ClubRobotiqueECAM/Balises/Photos/2015-09-10 11.16.47.jpg

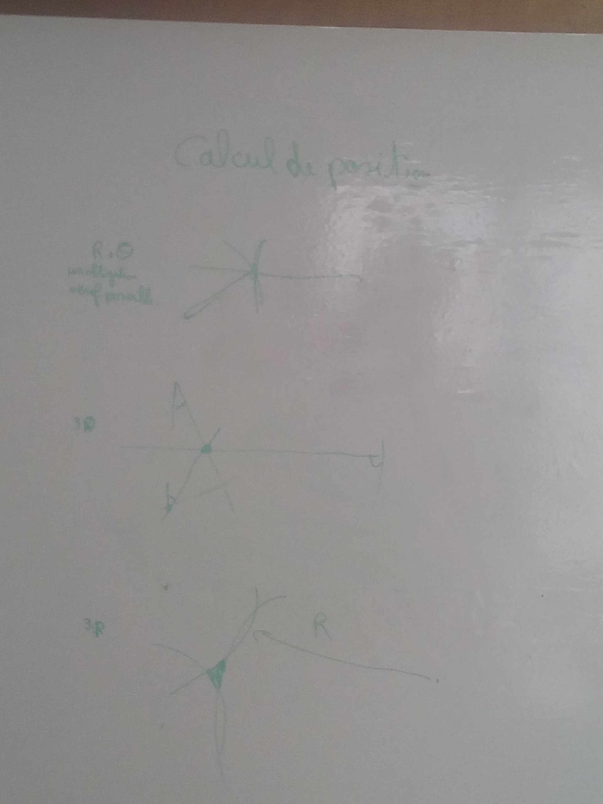
Photos/2015-09-10 11.16.47.jpg
