ClubRobotiqueECAM/Balises/Photos/2015-09-18 08.21.55.jpg

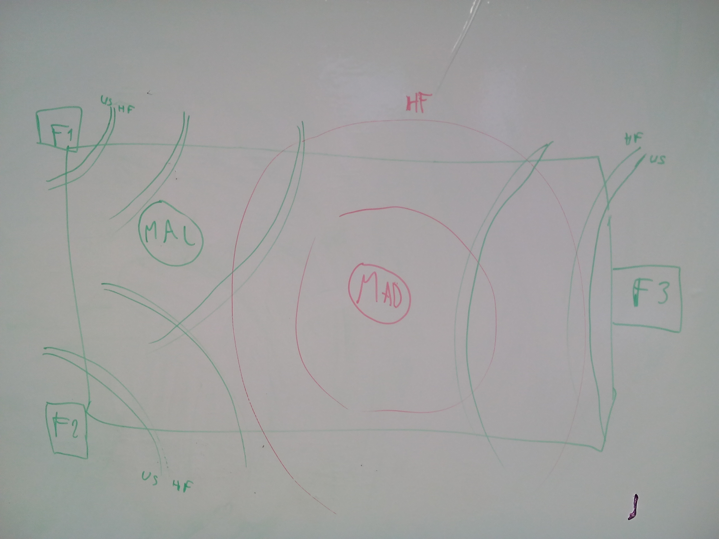
Photos/2015-09-18 08.21.55.jpg
