ClubRobotiqueECAM/Balises/Photos/2015-09-18 15.36.44.jpg

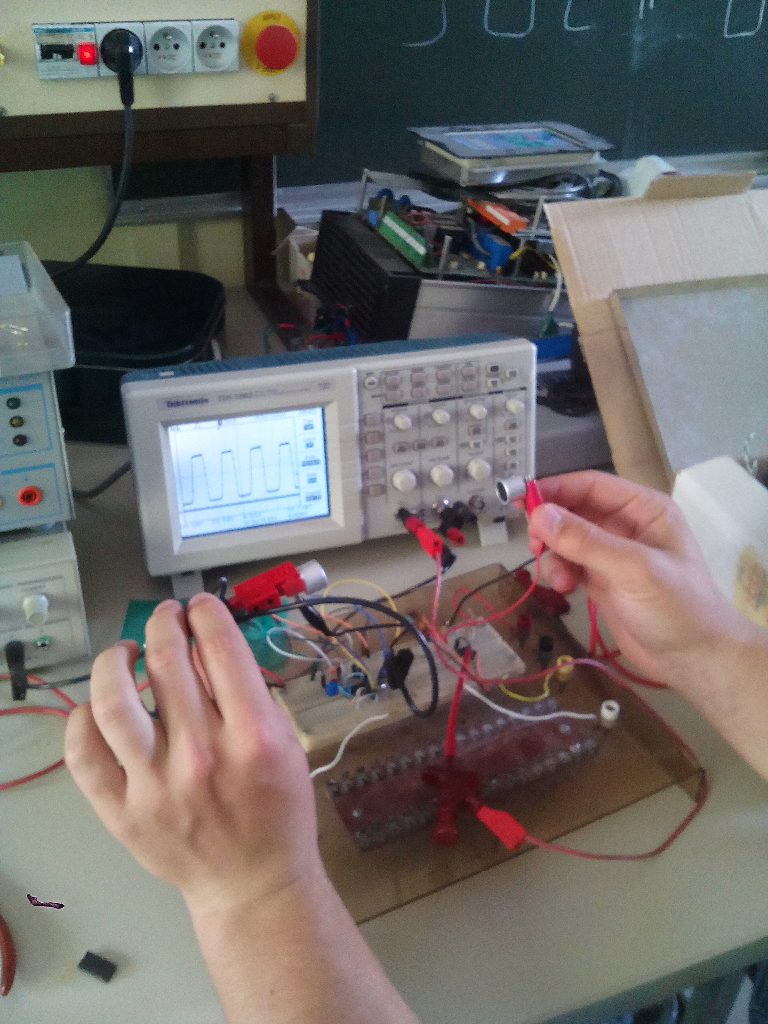
Photos/2015-09-18 15.36.44.jpg
