ClubRobotiqueECAM/Balises/Photos/2015-09-18 15.37.08.jpg

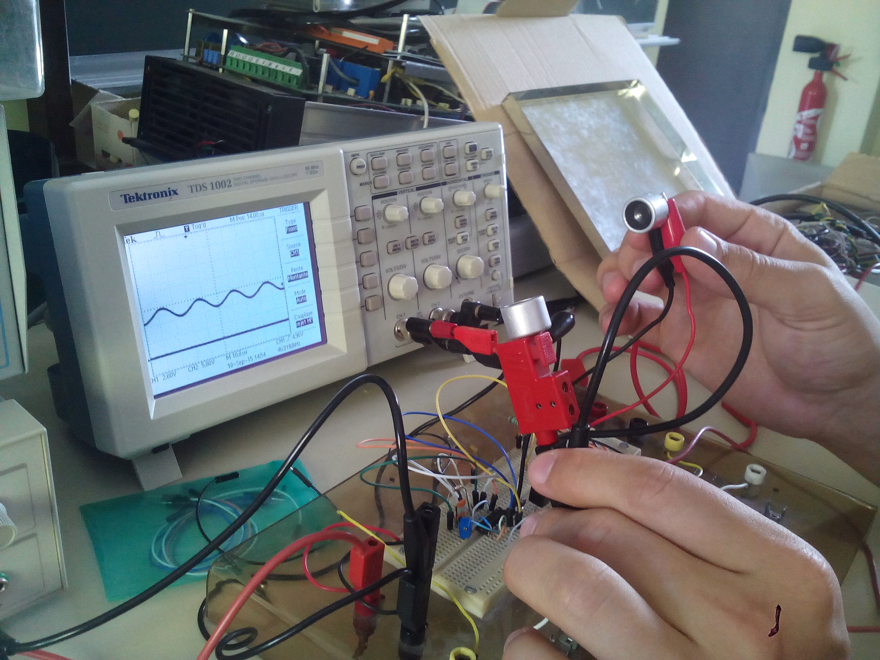
Photos/2015-09-18 15.37.08.jpg
