ClubRobotiqueECAM/Balises/Photos/2015-09-24 05-2 AO Proche.BMP

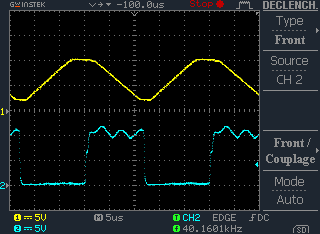
Photos/2015-09-24 05-2 AO Proche.BMP
