ClubRobotiqueECAM/Balises/Photos/2015-09-24 14.49.16.jpg

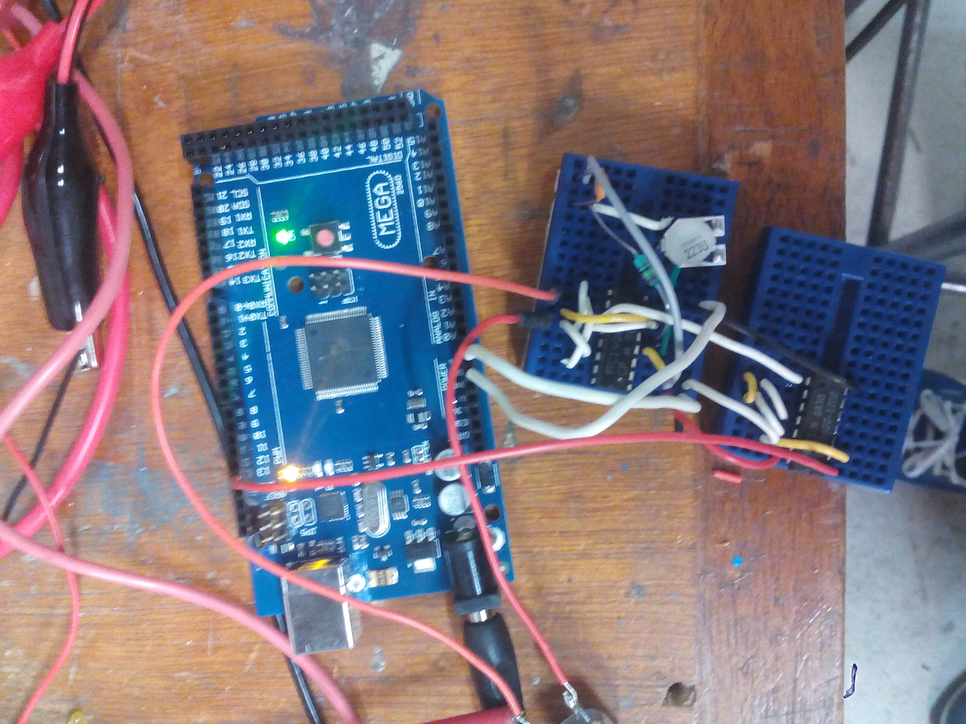
Photos/2015-09-24 14.49.16.jpg
