ClubRobotiqueECAM/Balises/Photos/2015-10-22 09.53.31.jpg

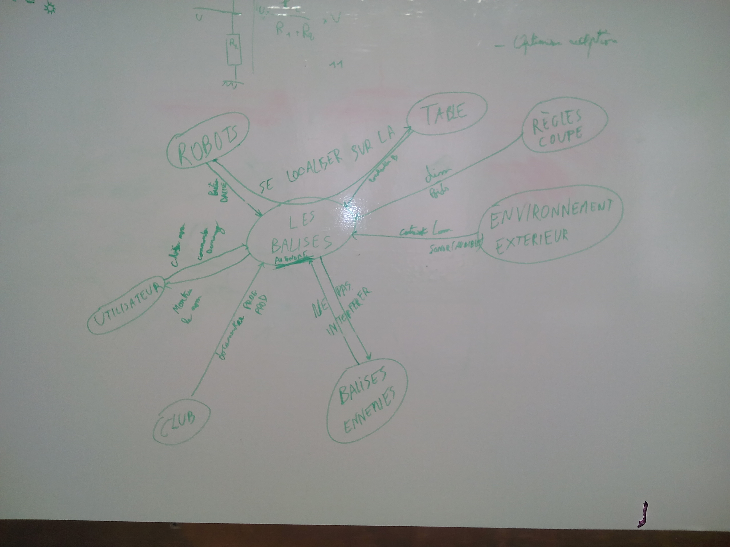
Photos/2015-10-22 09.53.31.jpg
