ClubRobotiqueECAM/Balises/Photos/2015-11-04 15.26.15.jpg

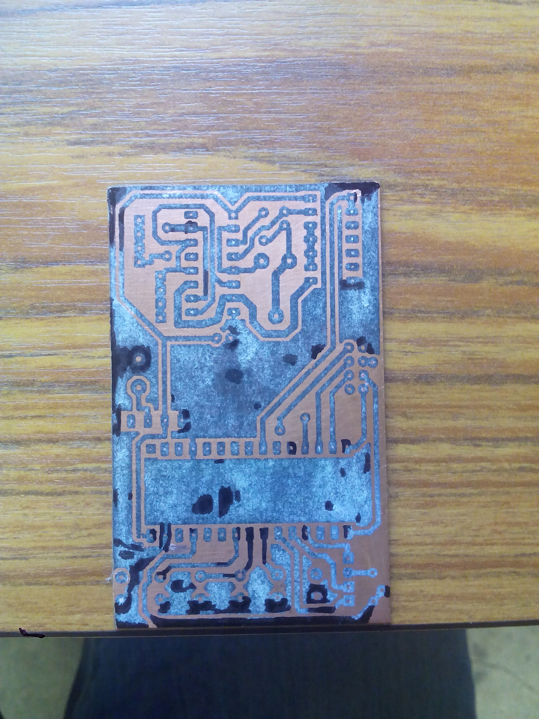
Photos/2015-11-04 15.26.15.jpg
