ClubRobotiqueECAM/Balises/Photos/2015-11-04 16.58.57.jpg

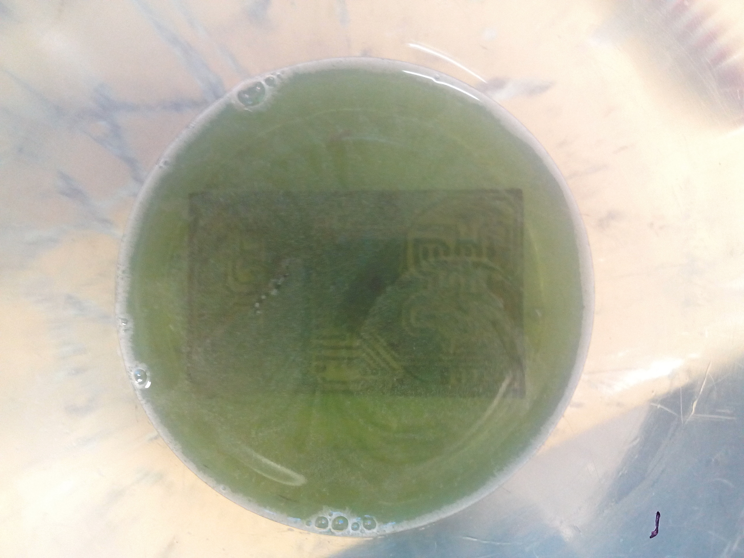
Photos/2015-11-04 16.58.57.jpg
