ClubRobotiqueECAM/Balises/Photos/2015-11-04 16.59.13.jpg

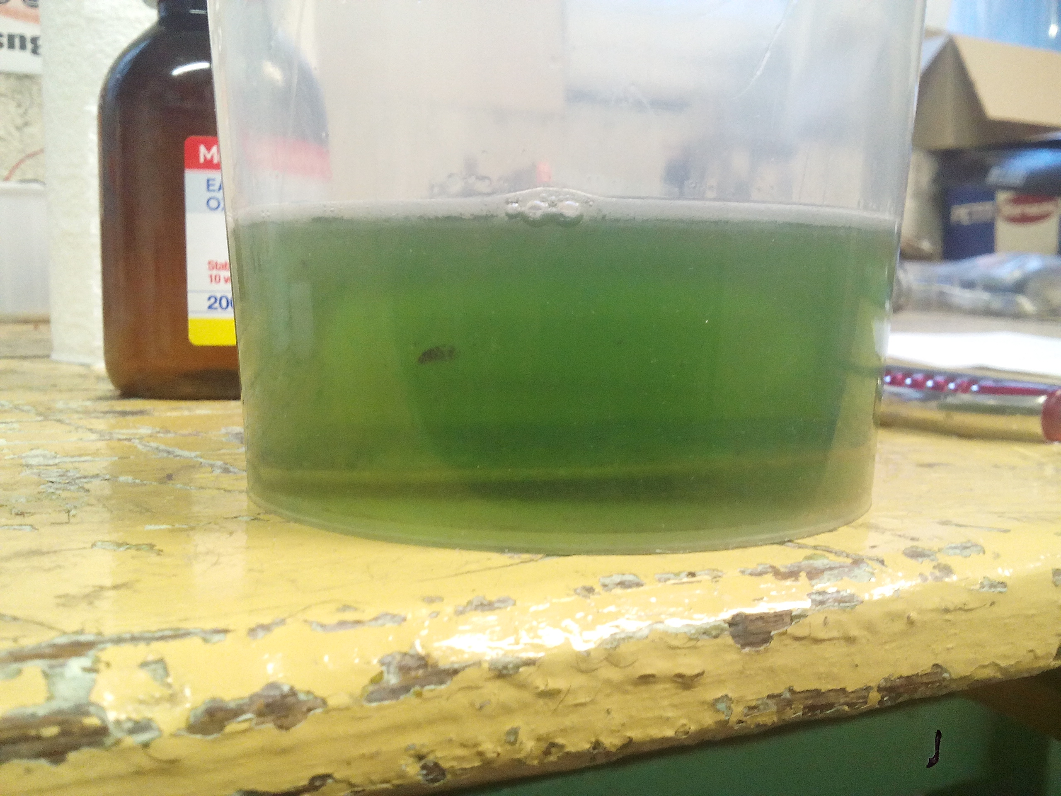
Photos/2015-11-04 16.59.13.jpg
