ClubRobotiqueECAM/Balises/Photos/2015-11-05 22.45.04.jpg

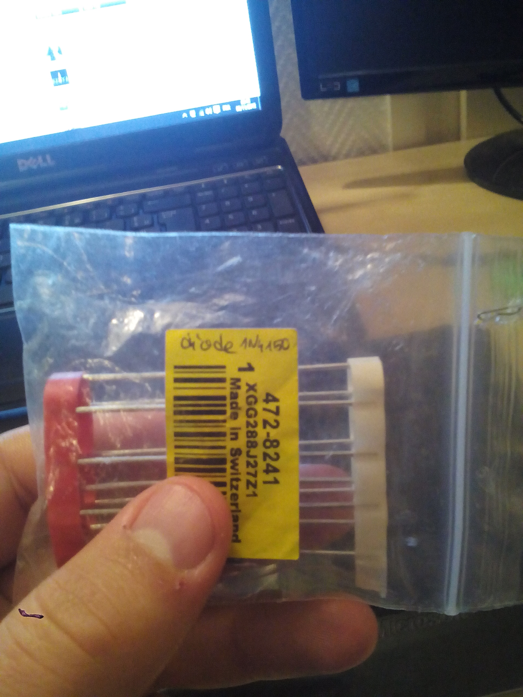
Photos/2015-11-05 22.45.04.jpg
