ClubRobotiqueECAM/Balises/Photos/2015-11-06 15.36.19.jpg

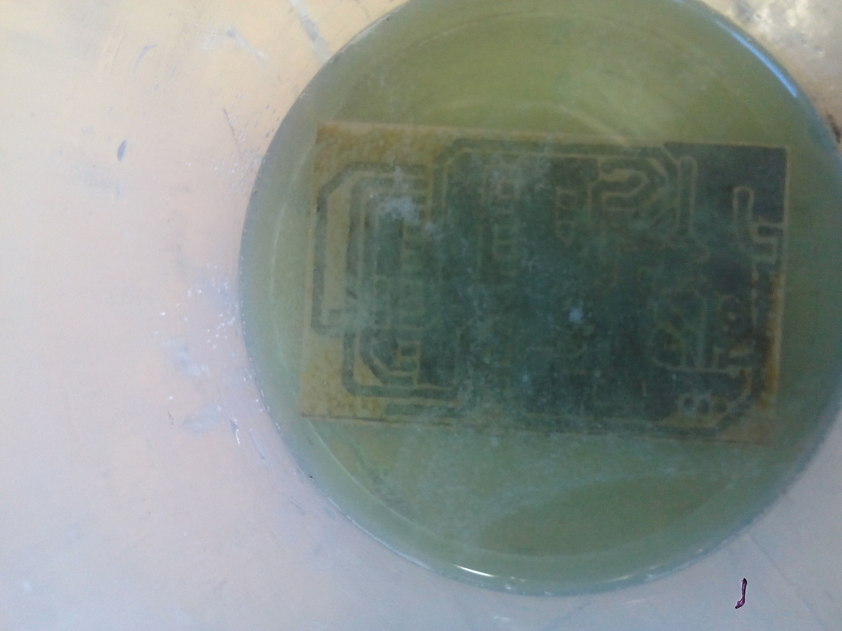
Photos/2015-11-06 15.36.19.jpg
