ClubRobotiqueECAM/Balises/Photos/2015-11-06 15.36.27.jpg

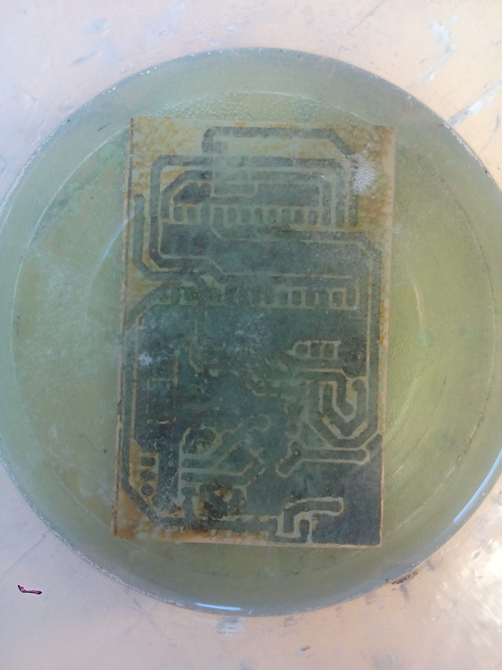
Photos/2015-11-06 15.36.27.jpg
