ClubRobotiqueECAM/Balises/Photos/2015-11-06 15.54.33.jpg

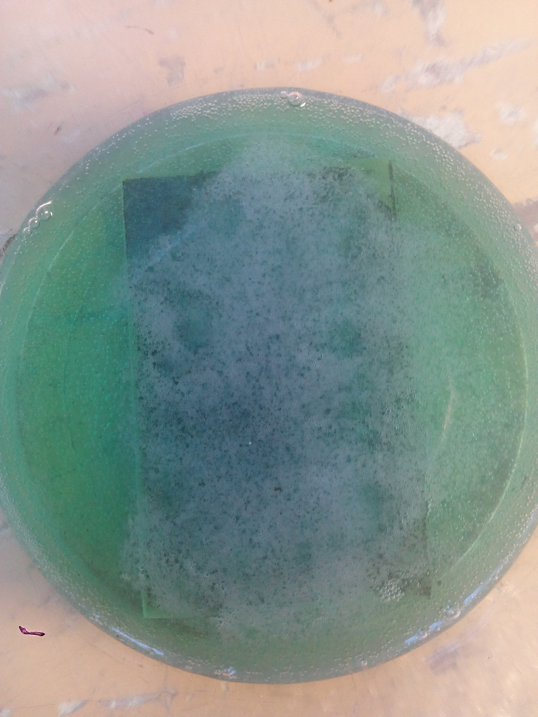
Photos/2015-11-06 15.54.33.jpg
