ClubRobotiqueECAM/Balises/Photos/2015-11-12 11.26.49.jpg

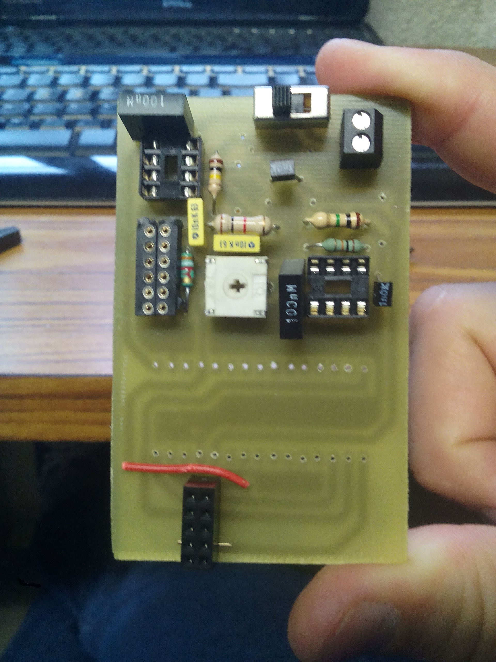
Photos/2015-11-12 11.26.49.jpg
