ClubRobotiqueECAM/Balises/Photos/2015-11-20 09.31.01 mot.jpg

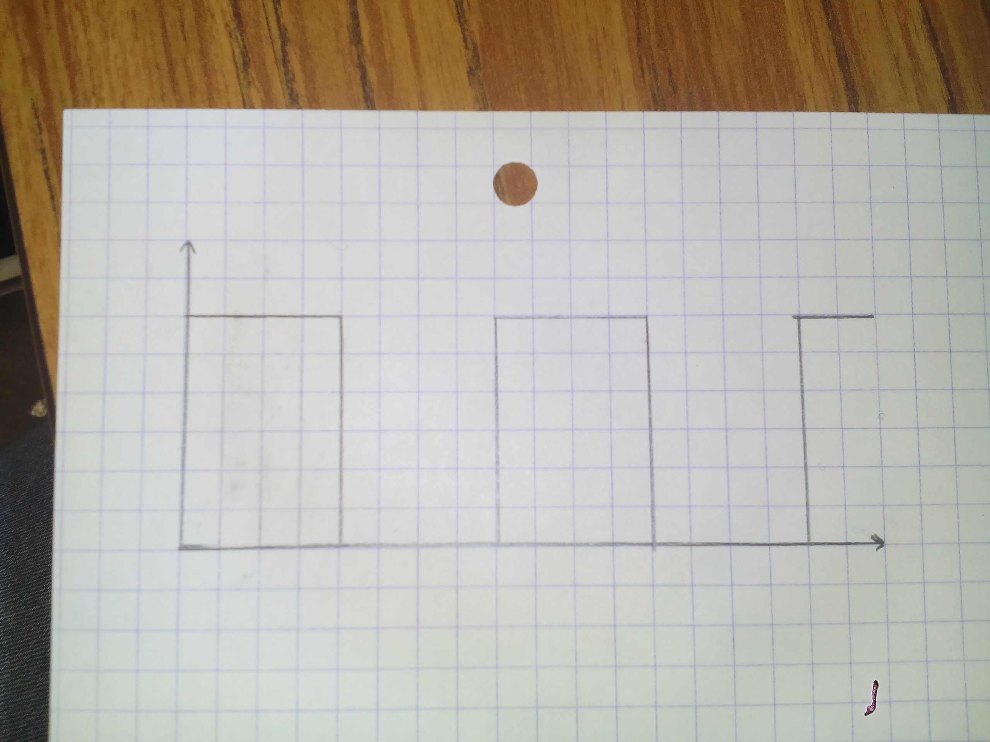
Photos/2015-11-20 09.31.01 mot.jpg
