ClubRobotiqueECAM/Balises/Photos/2015-11-20 09.34.17 porteuse.jpg

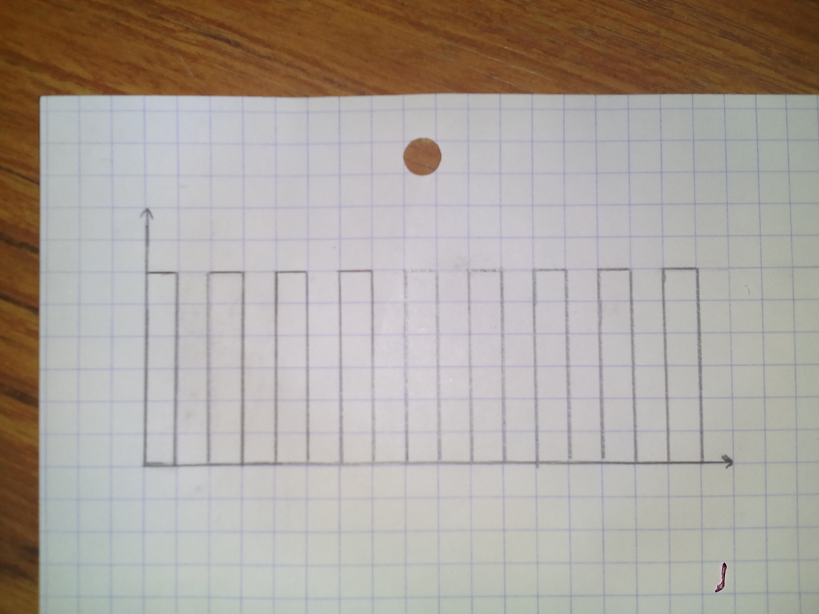
Photos/2015-11-20 09.34.17 porteuse.jpg
