ClubRobotiqueECAM/Balises/Photos/2015-11-20 09.36.22 modulation.jpg

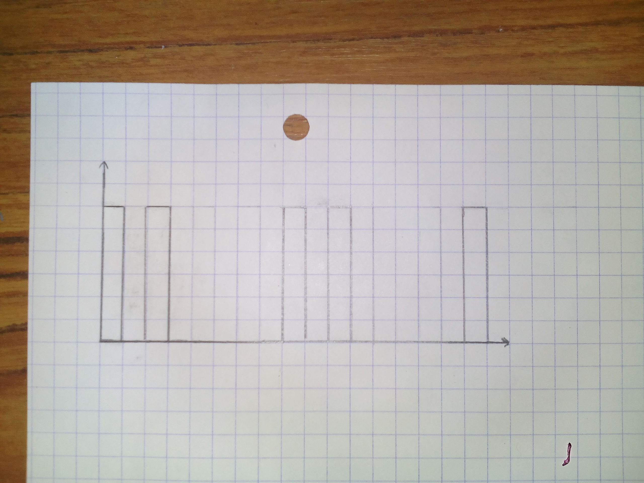
Photos/2015-11-20 09.36.22 modulation.jpg
