ClubRobotiqueECAM/Balises/Photos/2015-11-23 20.47.19.jpg

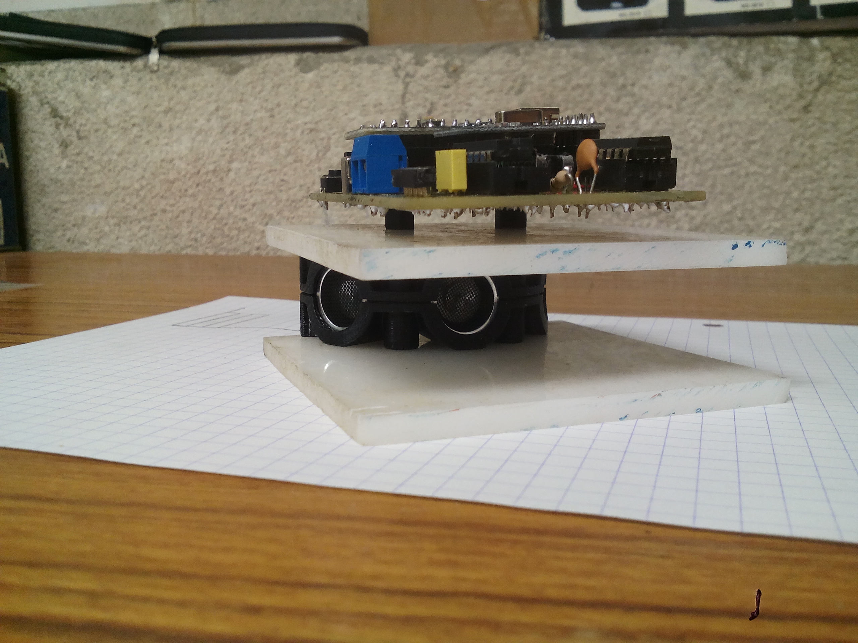
Photos/2015-11-23 20.47.19.jpg
