ClubRobotiqueECAM/Balises/Photos/2015-12-10 17h59.JPG

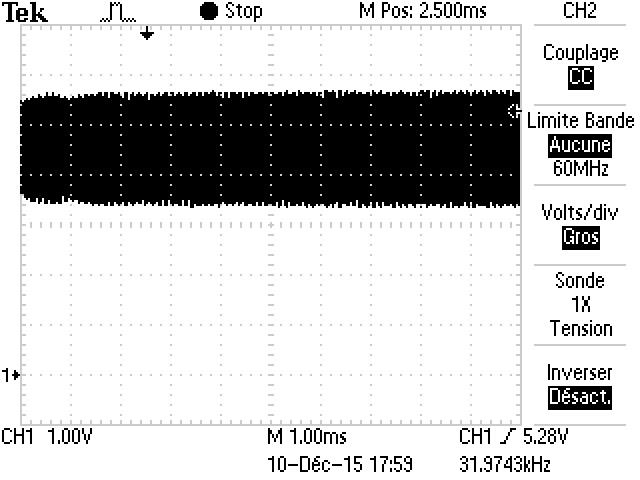
Photos/2015-12-10 17h59.JPG
