ClubRobotiqueECAM/Balises/Photos/2015-12-10 18h12.JPG

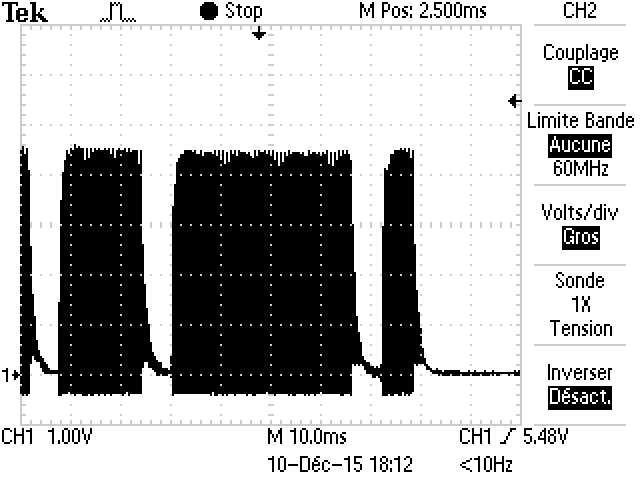
Photos/2015-12-10 18h12.JPG
