ClubRobotiqueECAM/Balises/Photos/2015-12-14 sortie avec 4,5v ref 2 à entendre.bmp

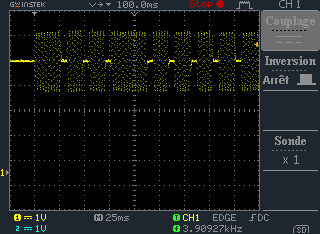
Photos/2015-12-14 sortie avec 4,5v ref 2 à entendre.bmp
