ClubRobotiqueECAM/Balises/Photos/2015-12-17 2emeteur.JPG

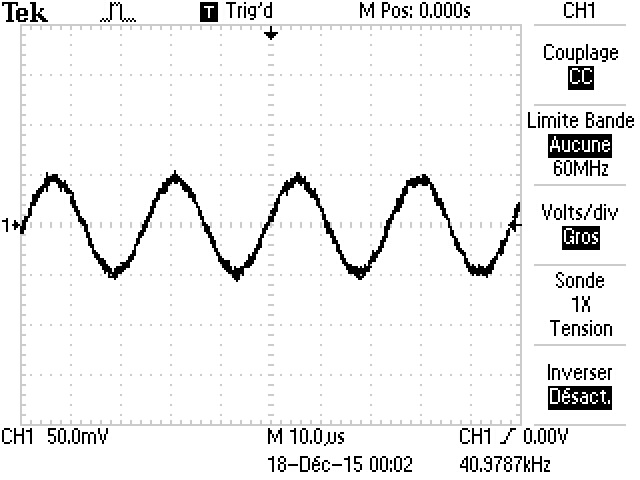
Photos/2015-12-17 2emeteur.JPG
