ClubRobotiqueECAM/Balises/Photos/2016-01-14 2.png

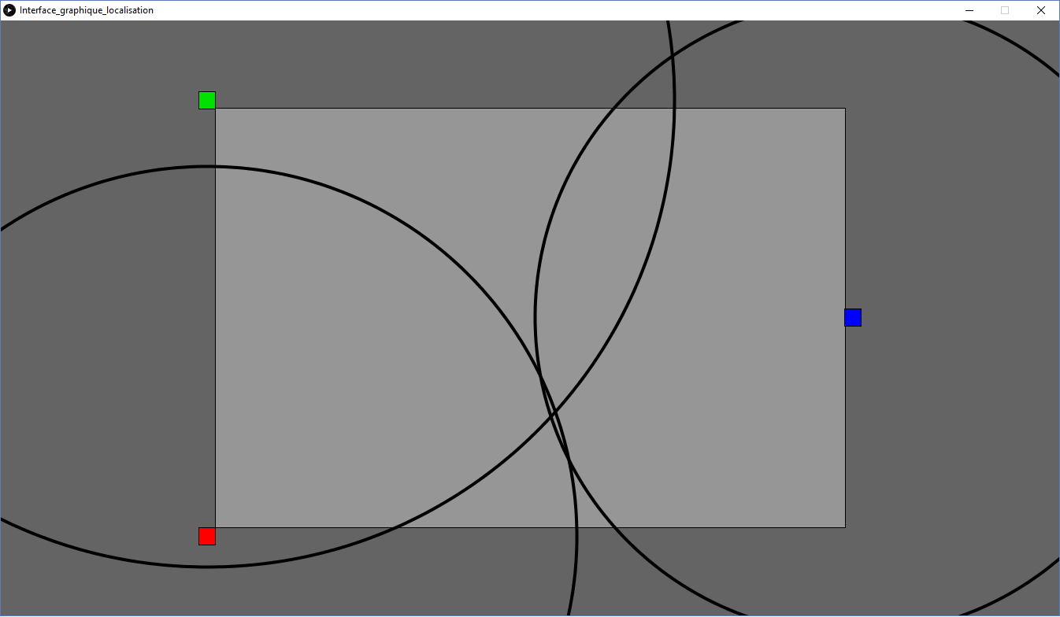
Photos/2016-01-14 2.png
