ClubRobotiqueECAM/Balises/Photos/2016-01-14 3.png

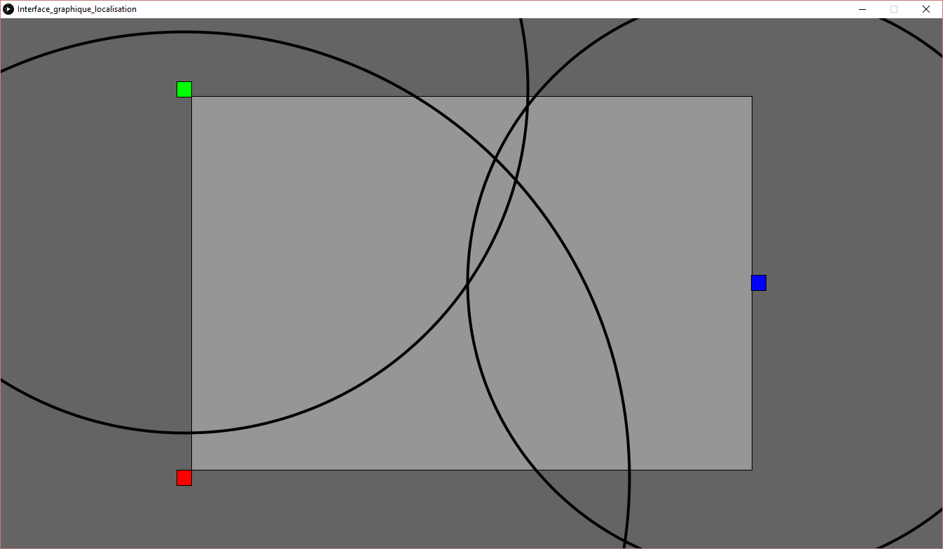
Photos/2016-01-14 3.png
