ClubRobotiqueECAM/Balises/Photos/2016-01-14 07.56.17.jpg

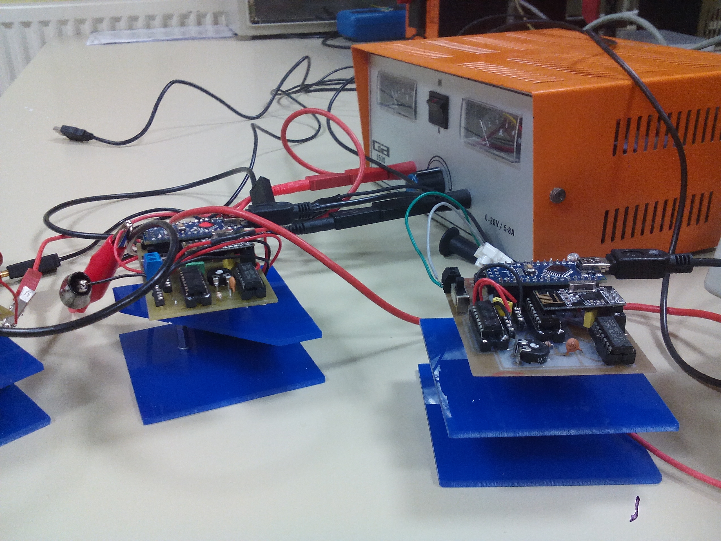
Photos/2016-01-14 07.56.17.jpg
