ClubRobotiqueECAM/Balises/Photos/2016-01-14 07.jpg

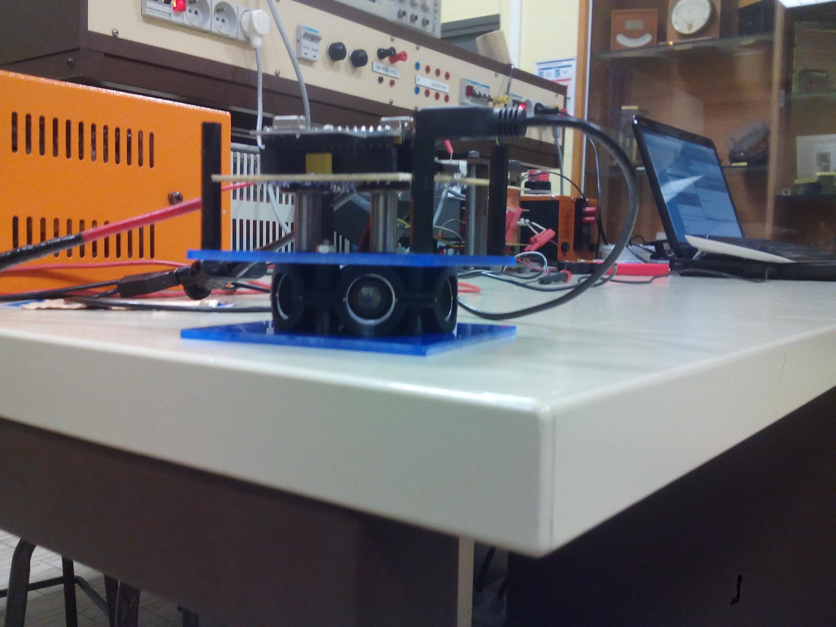
Photos/2016-01-14 07.jpg
