ClubRobotiqueECAM/Balises/Photos/2016-01-14 10.05.29.jpg

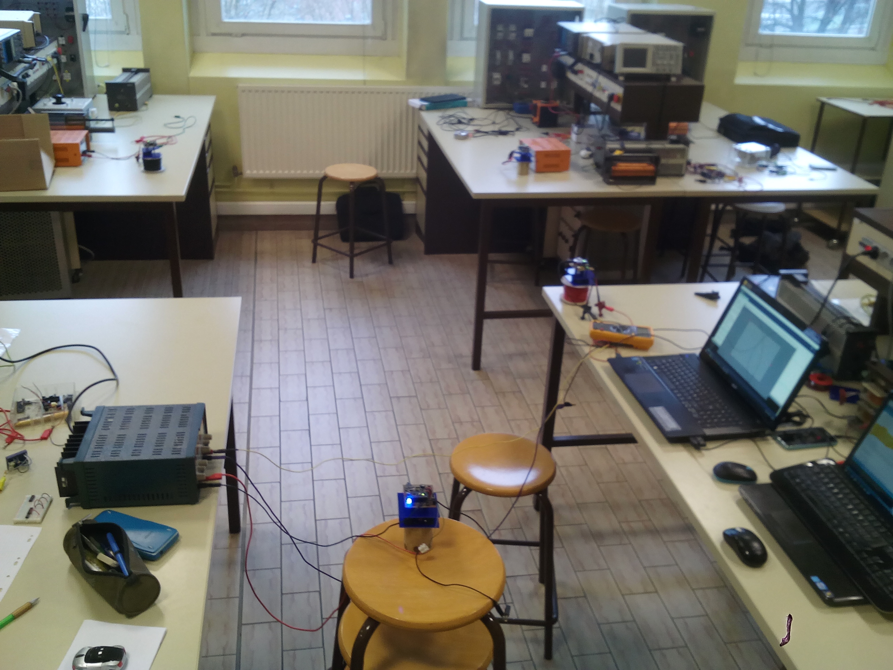
Photos/2016-01-14 10.05.29.jpg
