ClubRobotiqueECAM/Balises/Photos/2016-01-14 14.20.16.jpg

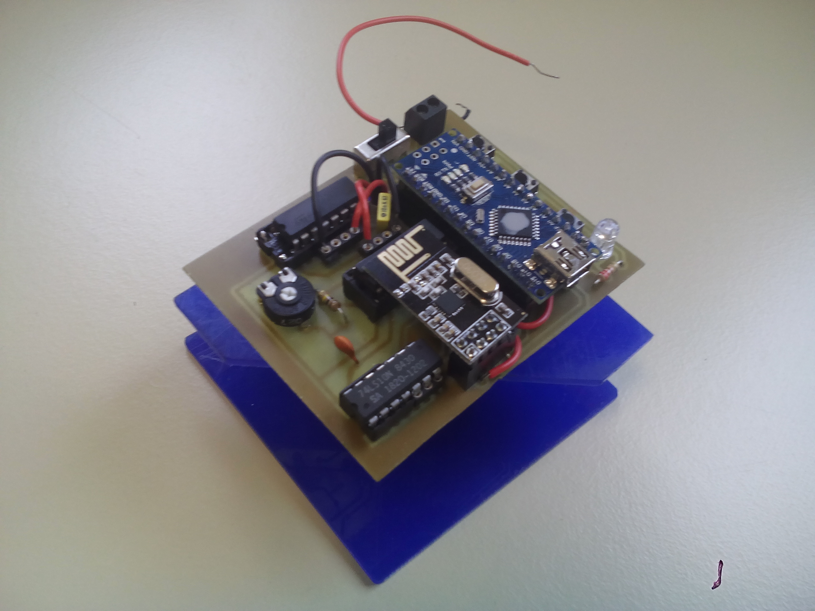
Photos/2016-01-14 14.20.16.jpg
