ClubRobotiqueECAM/Balises/Photos/2016-01-14.png

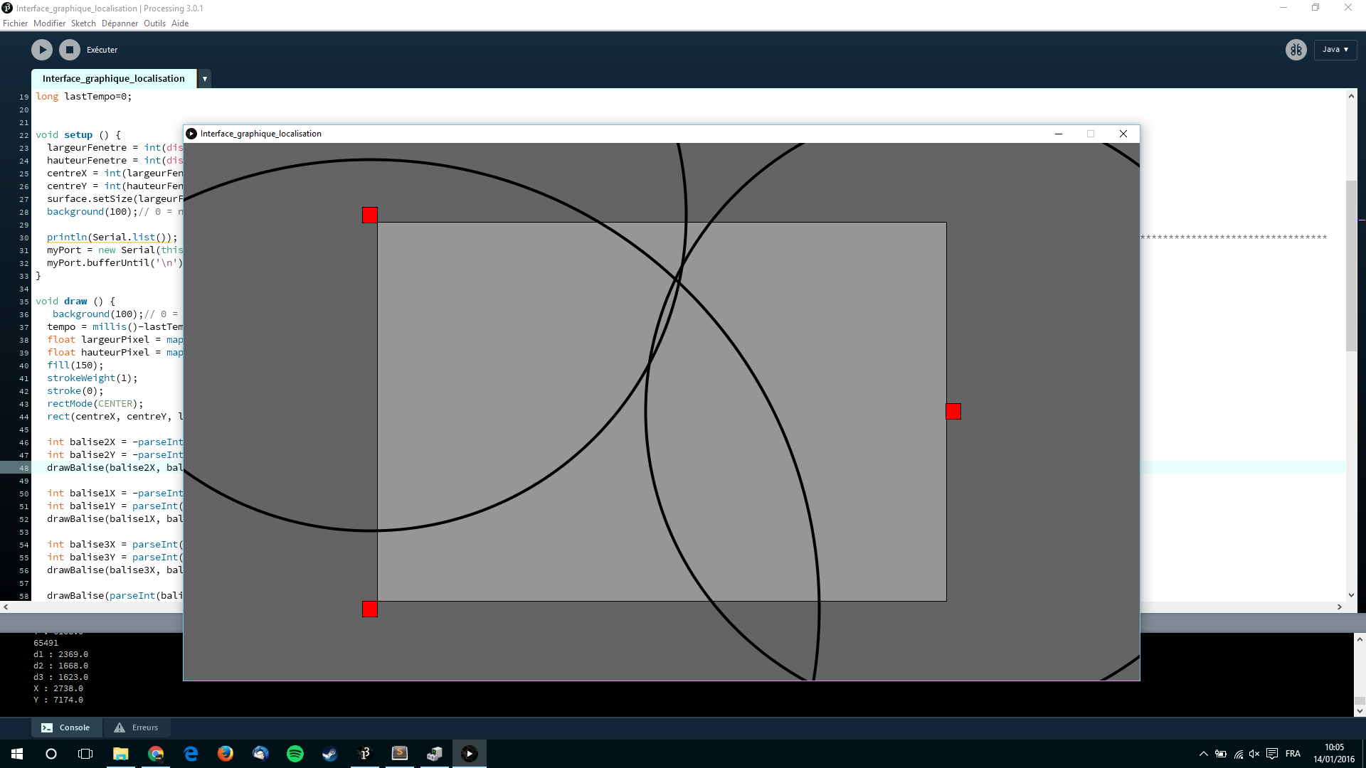
Photos/2016-01-14.png
