ClubRobotiqueECAM/Balises/Photos/IMG_20160108_095941.jpg

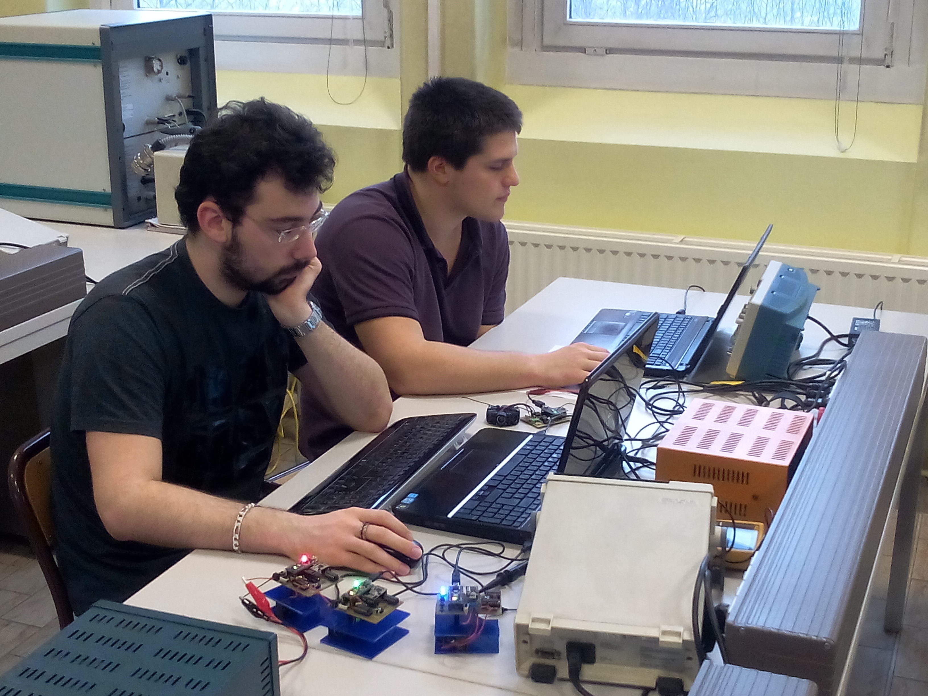
Photos/IMG_20160108_095941.jpg
