ClubRobotiqueECAM/Balises/Rapport/Fichiers supports/2015-11-20 09.36.22 modulation.jpg

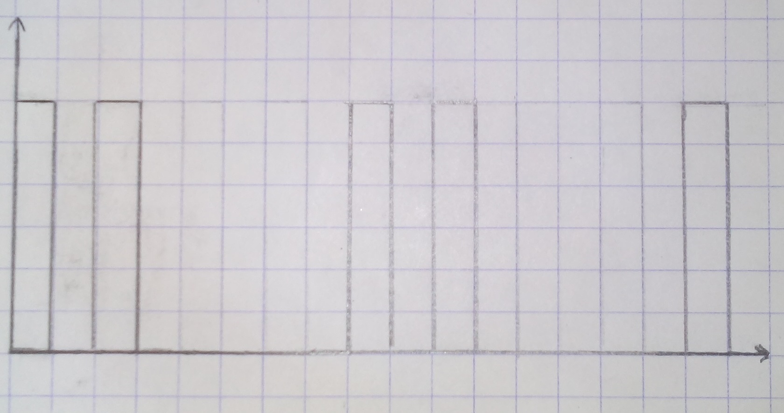
Rapport/Fichiers supports/2015-11-20 09.36.22 modulation.jpg
