ClubRobotiqueECAM/Balises/Rapport/Fichiers supports/ImagesElec/E1 40KHz.bmp

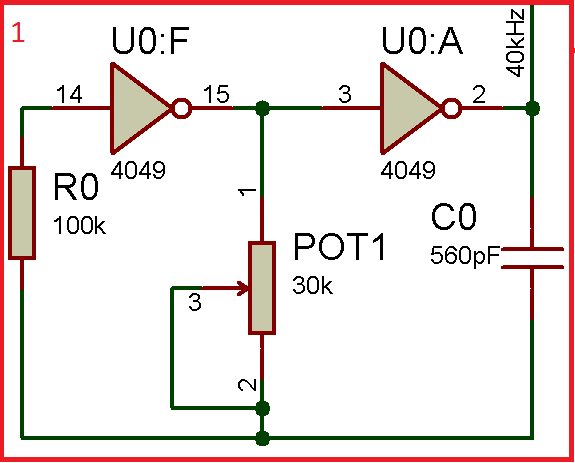
Rapport/Fichiers supports/ImagesElec/E1 40KHz.bmp
