ClubRobotiqueECAM/Balises/Rapport/Fichiers supports/ImagesElec/E2 Modulation.bmp

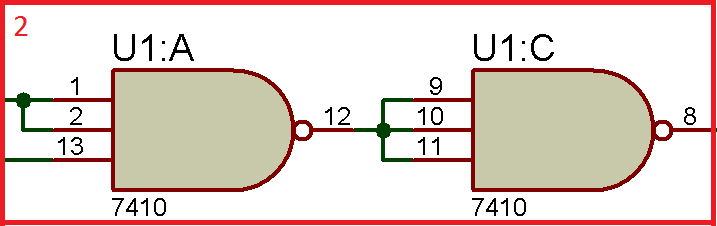
Rapport/Fichiers supports/ImagesElec/E2 Modulation.bmp
