ClubRobotiqueECAM/Balises/Rapport/Fichiers supports/ImagesElec/E3 Amplitude.bmp

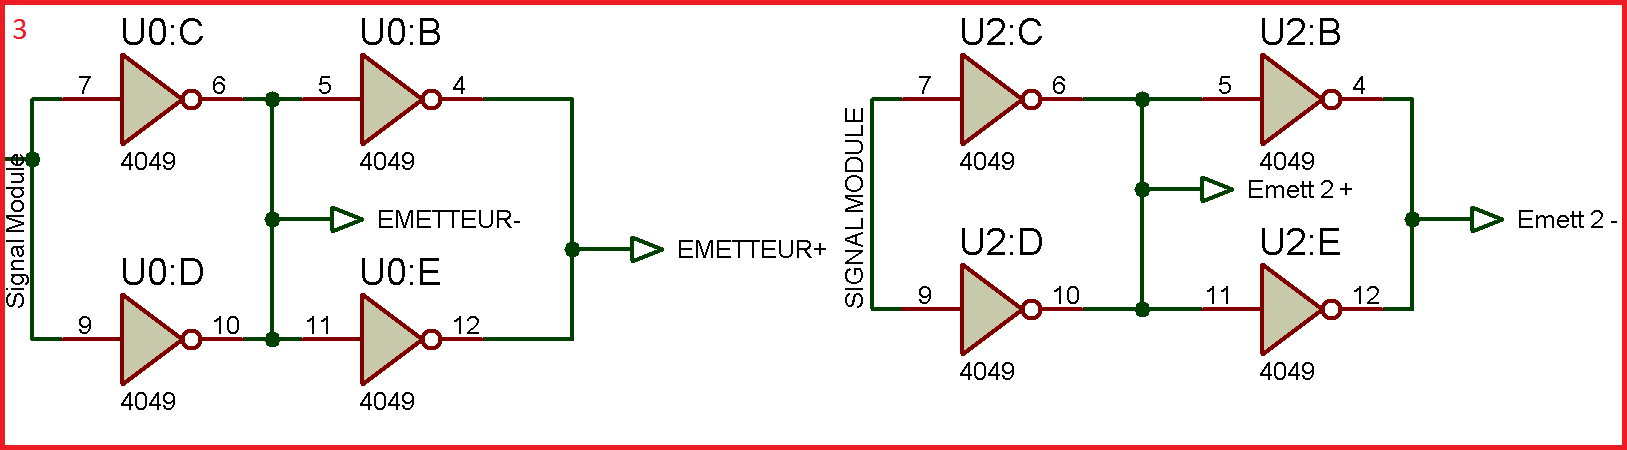
Rapport/Fichiers supports/ImagesElec/E3 Amplitude.bmp
