ClubRobotiqueECAM/Balises/Rapport/Fichiers supports/ImagesElec/E4 Borniers.bmp

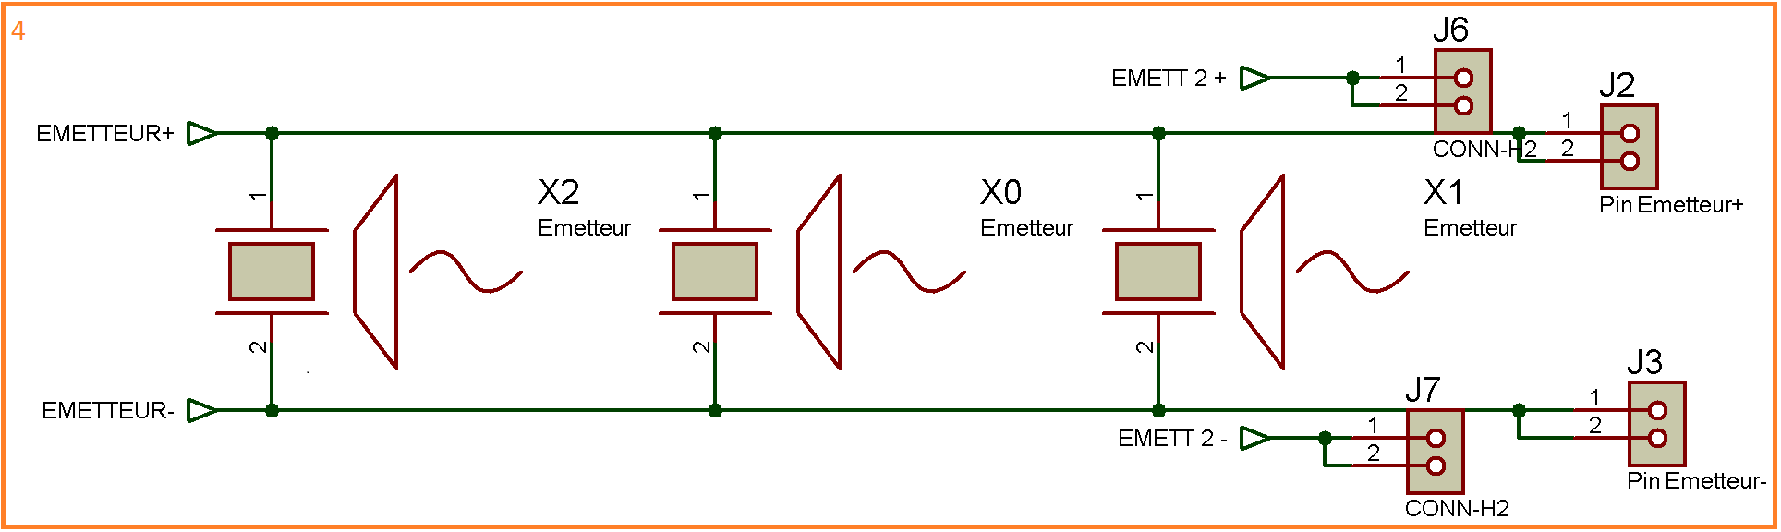
Rapport/Fichiers supports/ImagesElec/E4 Borniers.bmp
