ClubRobotiqueECAM/Balises/Rapport/Fichiers supports/ImagesElec/E5 LED Temoin.bmp

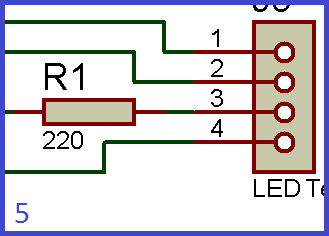
Rapport/Fichiers supports/ImagesElec/E5 LED Temoin.bmp
