ClubRobotiqueECAM/Balises/Rapport/Fichiers supports/ImagesElec/E6 SelectionNum.bmp

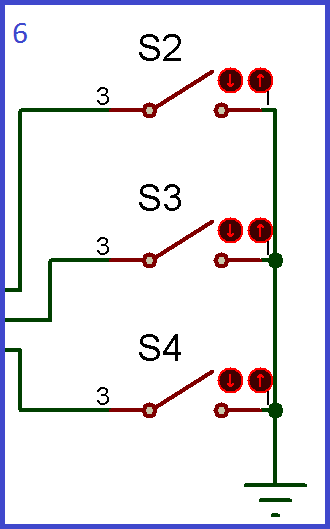
Rapport/Fichiers supports/ImagesElec/E6 SelectionNum.bmp
