ClubRobotiqueECAM/Balises/Rapport/Fichiers supports/ImagesElec/EAlim.bmp

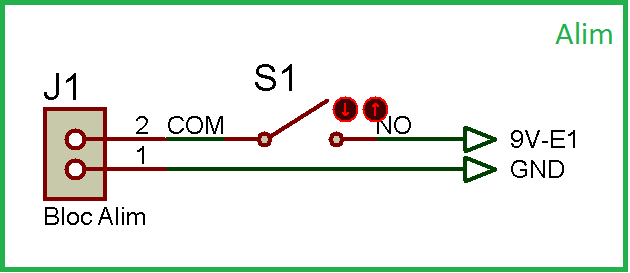
Rapport/Fichiers supports/ImagesElec/EAlim.bmp
