ClubRobotiqueECAM/Balises/Rapport/Fichiers supports/ImagesElec/R1 Borniers.bmp

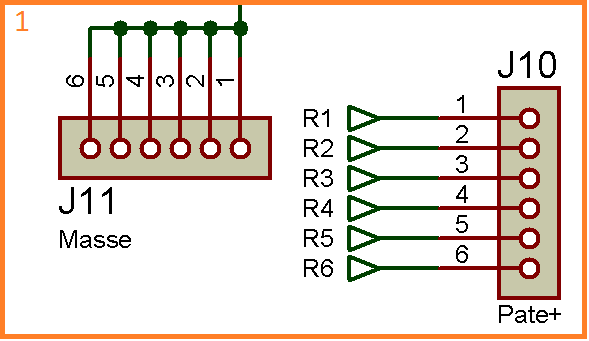
Rapport/Fichiers supports/ImagesElec/R1 Borniers.bmp
