ClubRobotiqueECAM/Balises/Rapport/Fichiers supports/ImagesElec/R2 Sommateur+4,5 x20.bmp

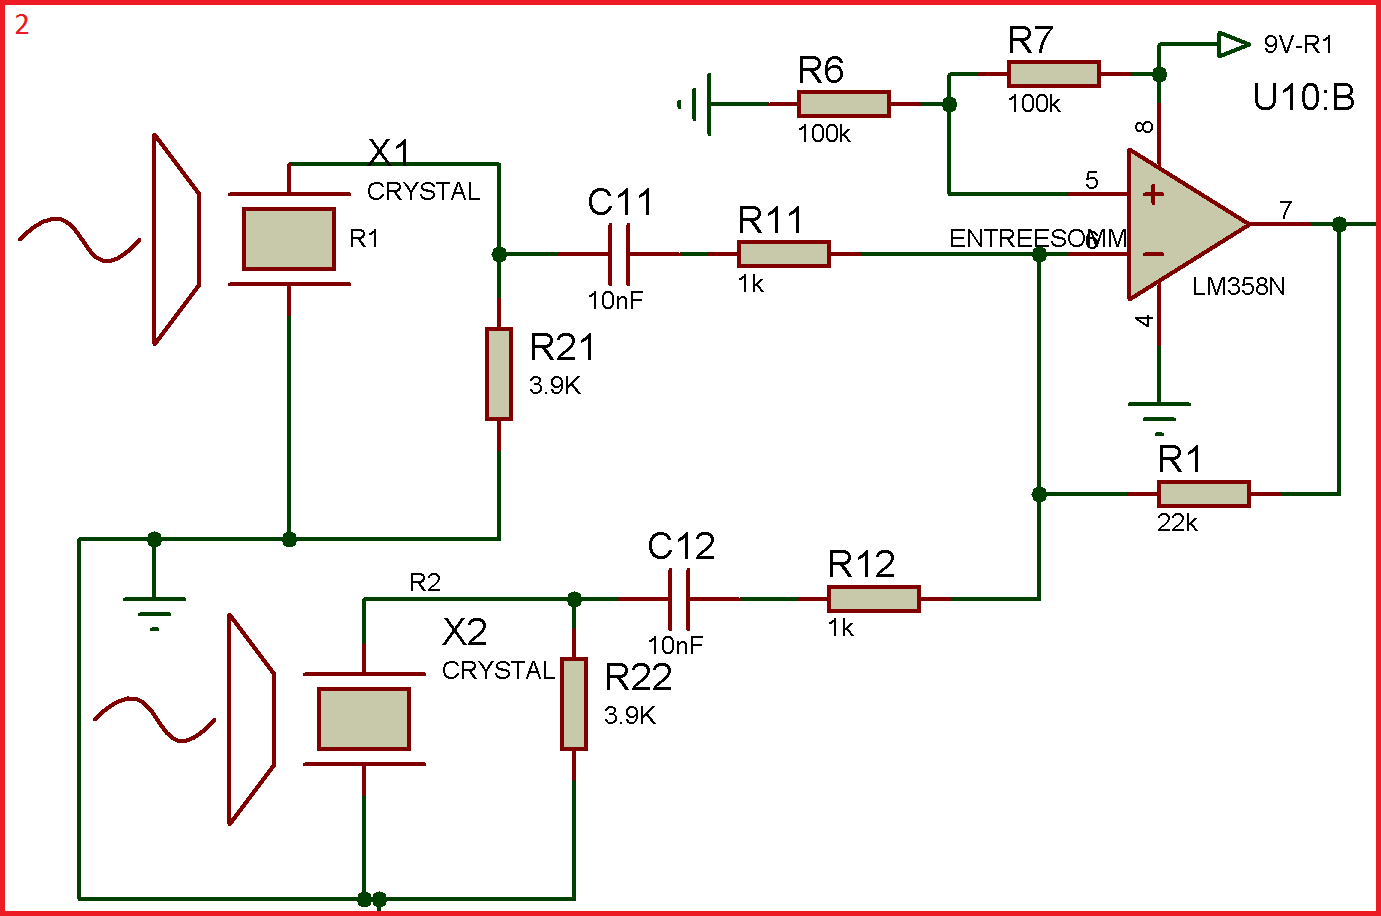
Rapport/Fichiers supports/ImagesElec/R2 Sommateur+4,5 x20.bmp
