ClubRobotiqueECAM/Balises/Rapport/Fichiers supports/ImagesElec/R5 filtre 40khz.bmp

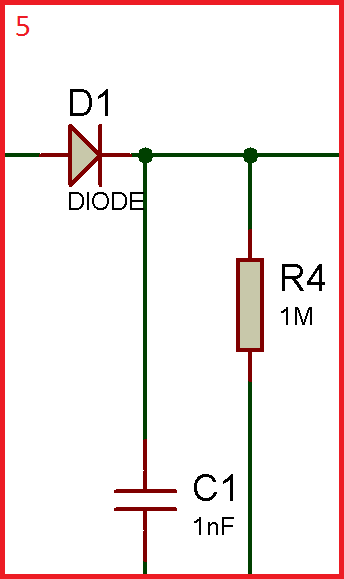
Rapport/Fichiers supports/ImagesElec/R5 filtre 40khz.bmp
