ClubRobotiqueECAM/Balises/Rapport/Fichiers supports/ImagesElec/R7 HF.bmp

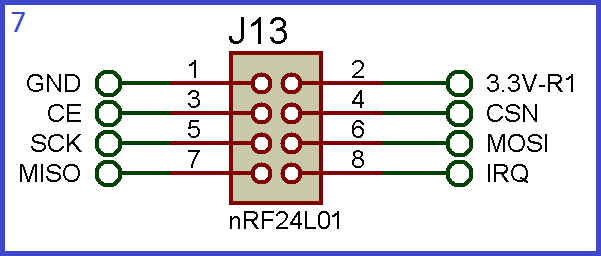
Rapport/Fichiers supports/ImagesElec/R7 HF.bmp
