ClubRobotiqueECAM/Balises/Ressources/Arduino_Nano_V3.0.png

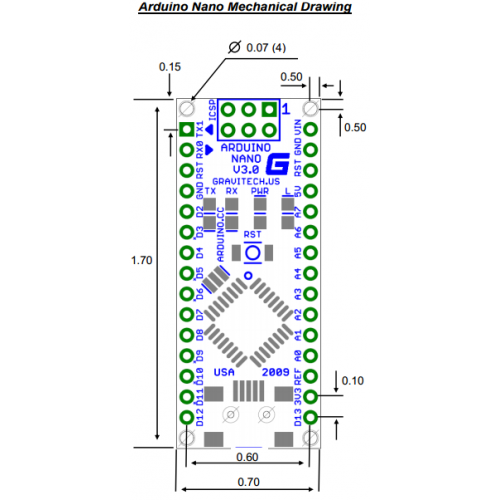
Ressources/Arduino_Nano_V3.0.png
