ClubRobotiqueECAM/Balises/Archives/rapport balises/schemas_pdf/alim4_seuil.pdf

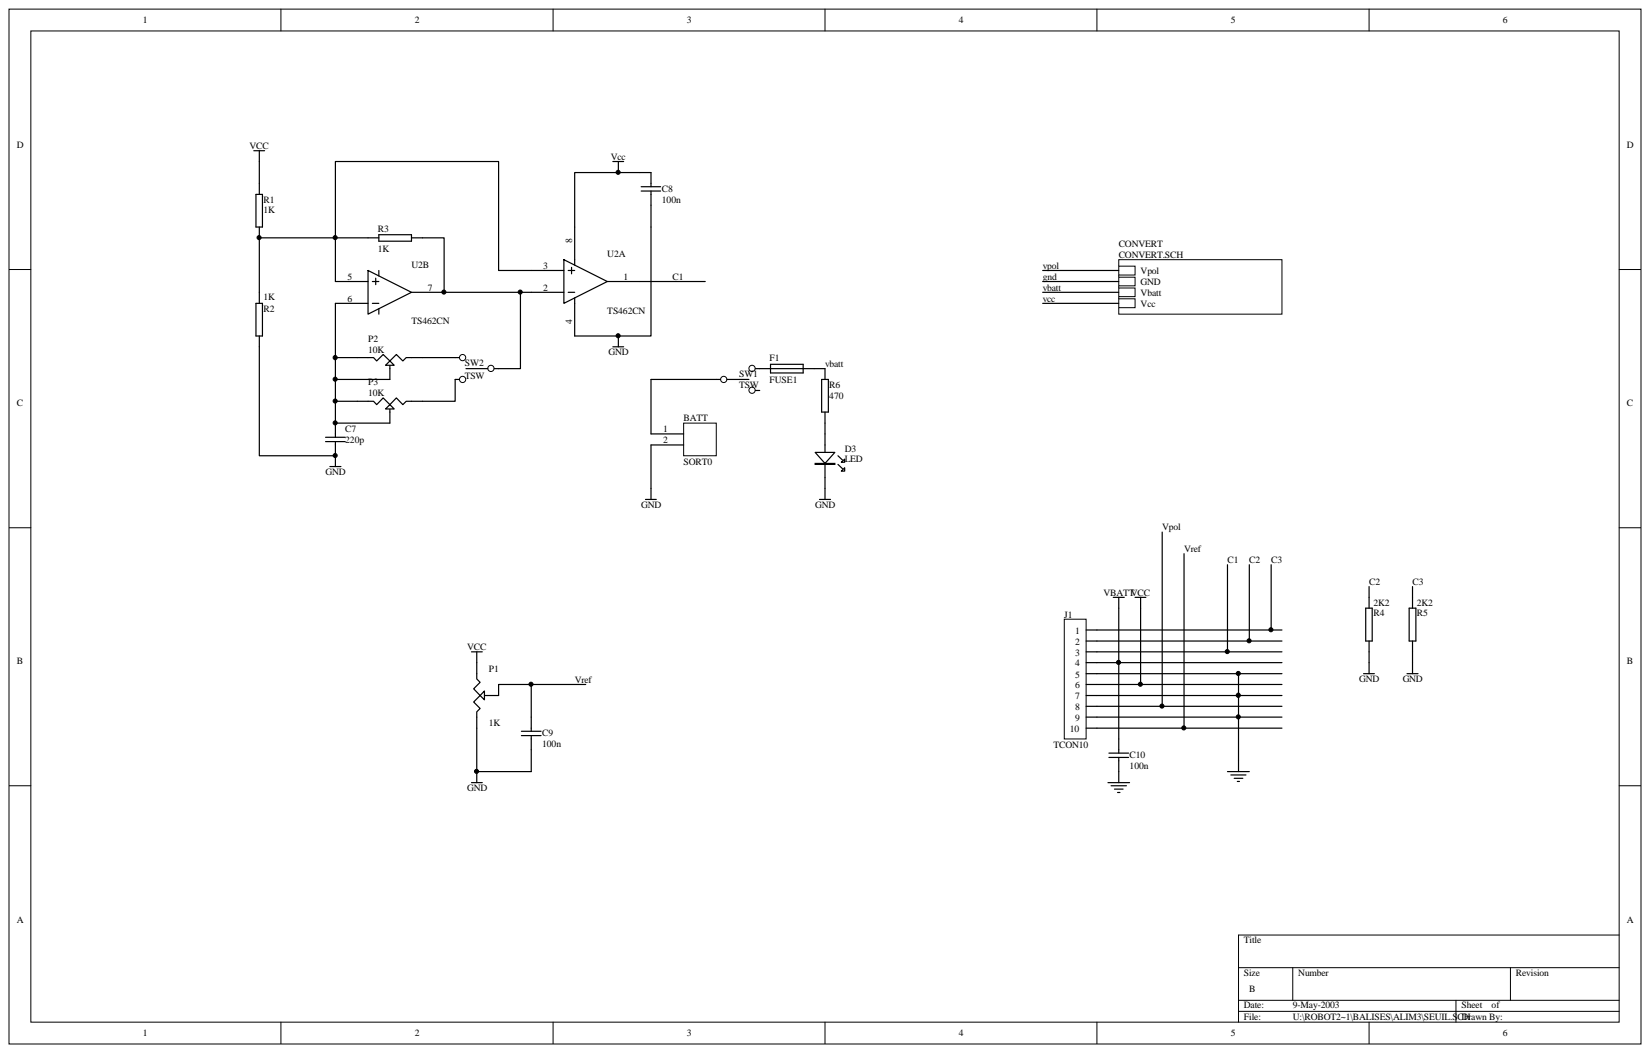
[picture p116: page 1]
