ClubRobotiqueECAM/Balises/Archives/rapport balises/schemas_pdf/balise_traitement.pdf

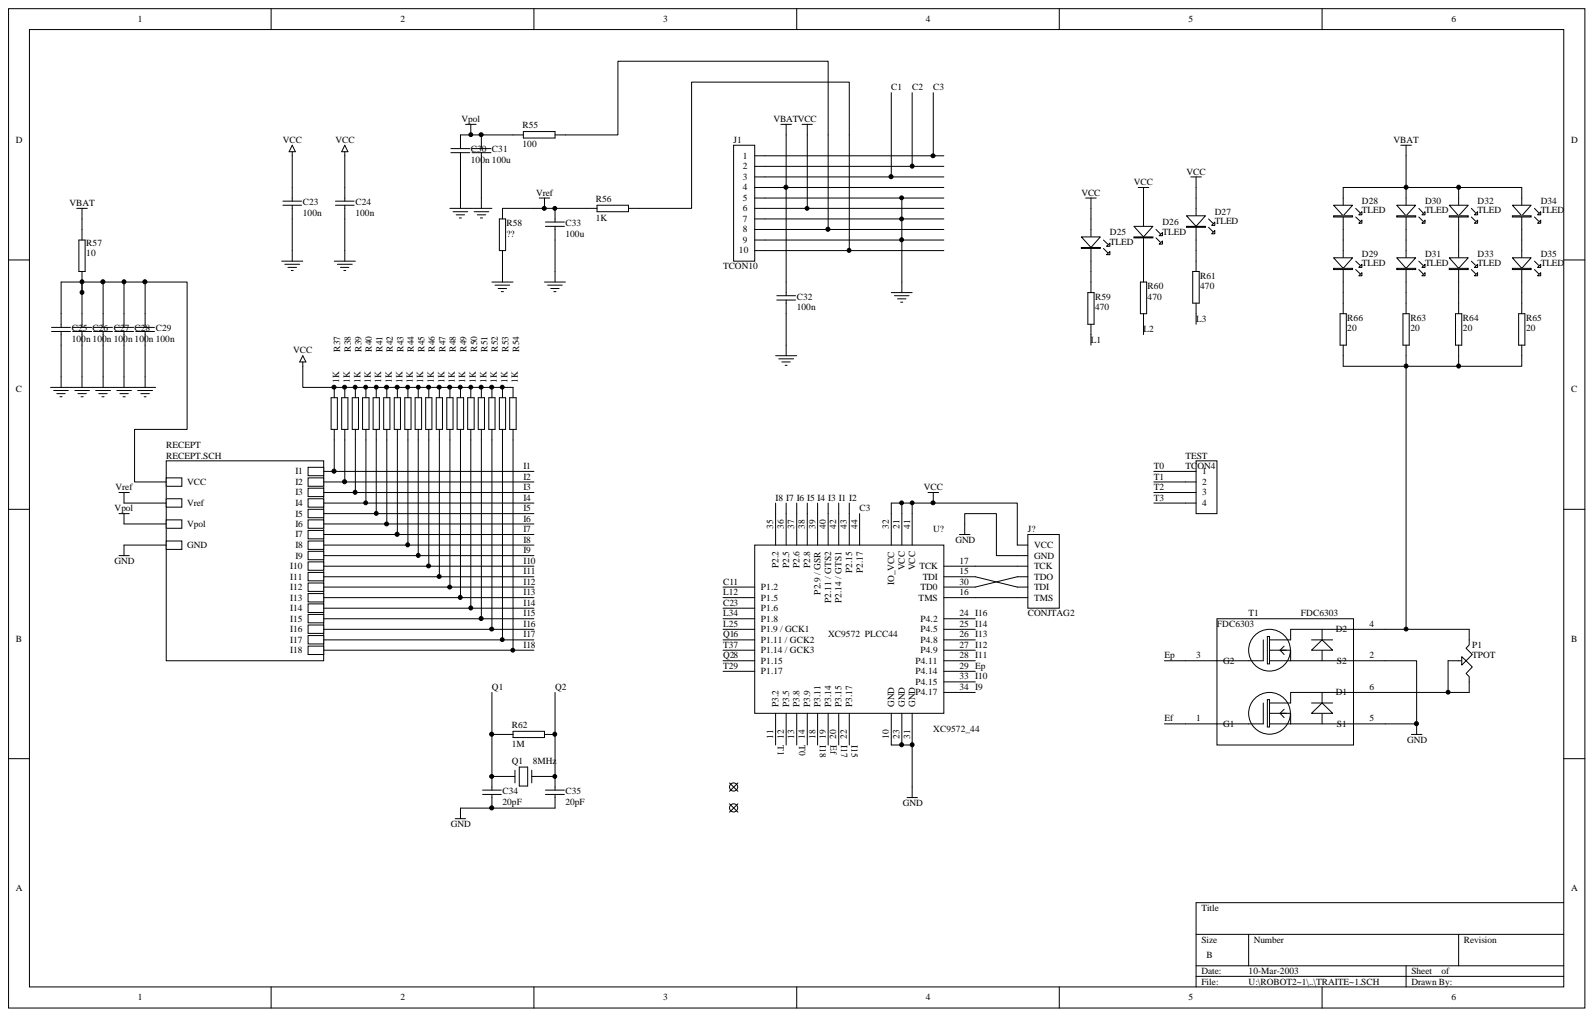
[picture p117: page 1]
