ClubRobotiqueECAM/Balises/Archives/rapport balises/schemas_pdf/robot_sch.pdf

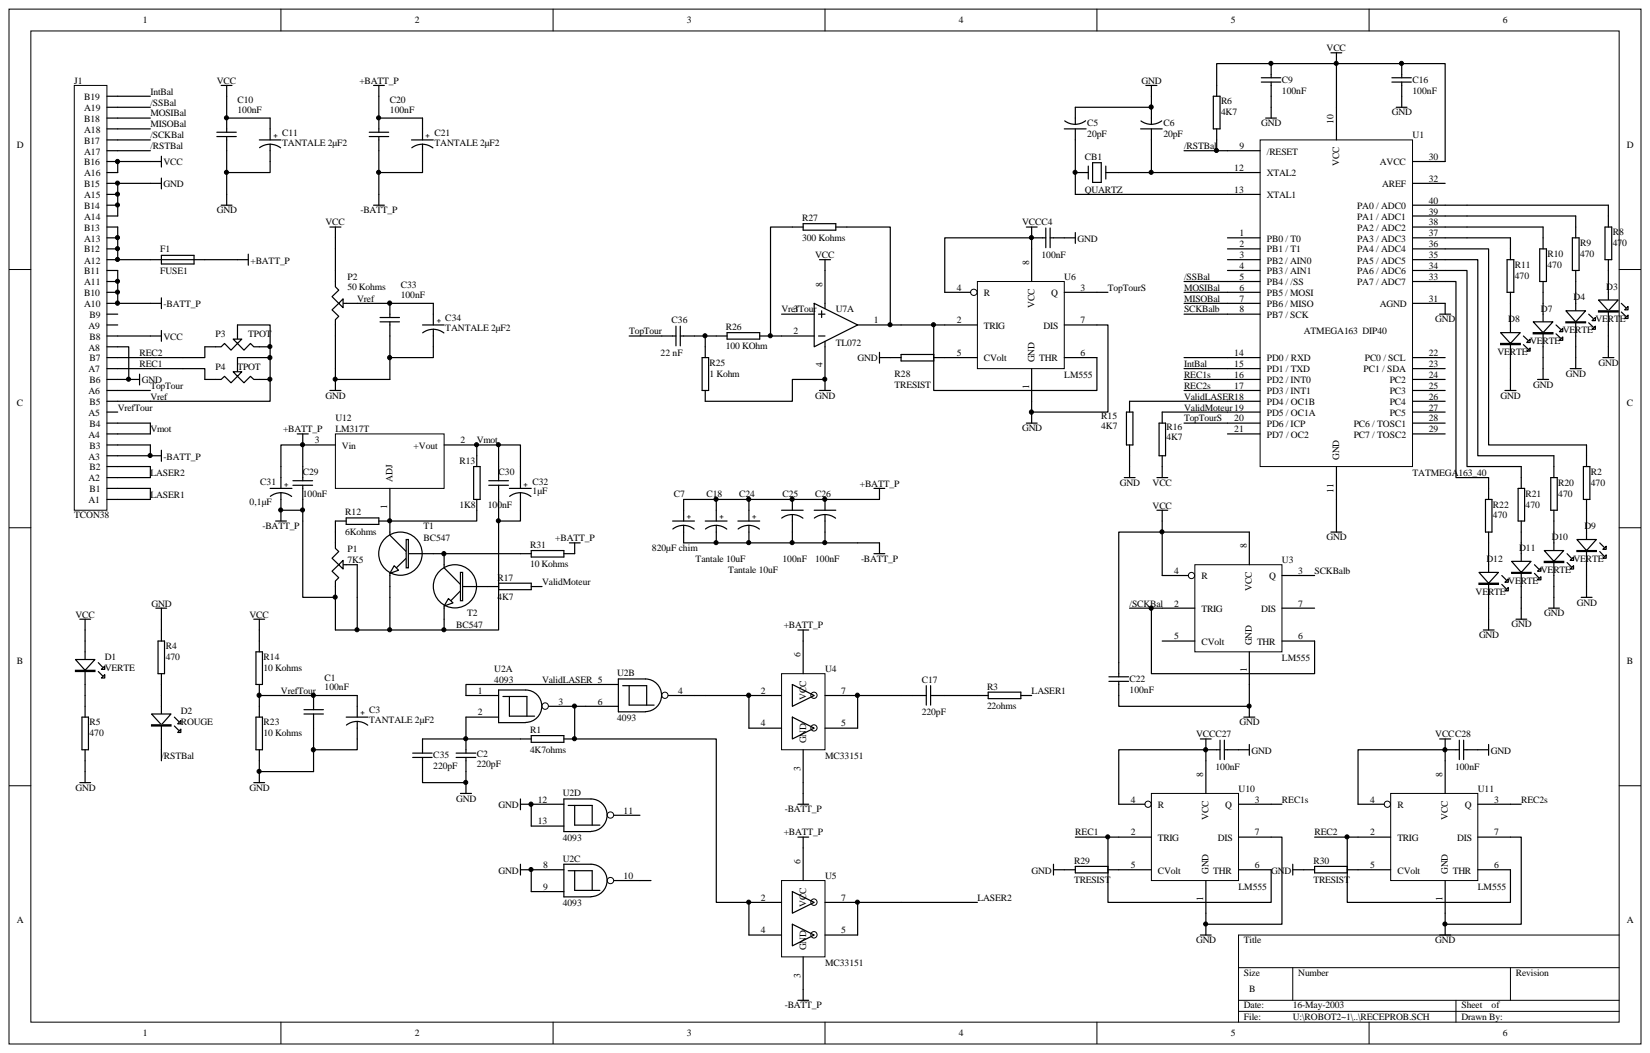
[picture p118: page 1]
