ClubRobotiqueECAM/Balises/Archives/rapport balises/schemas_pdf/tourelle_schema.pdf

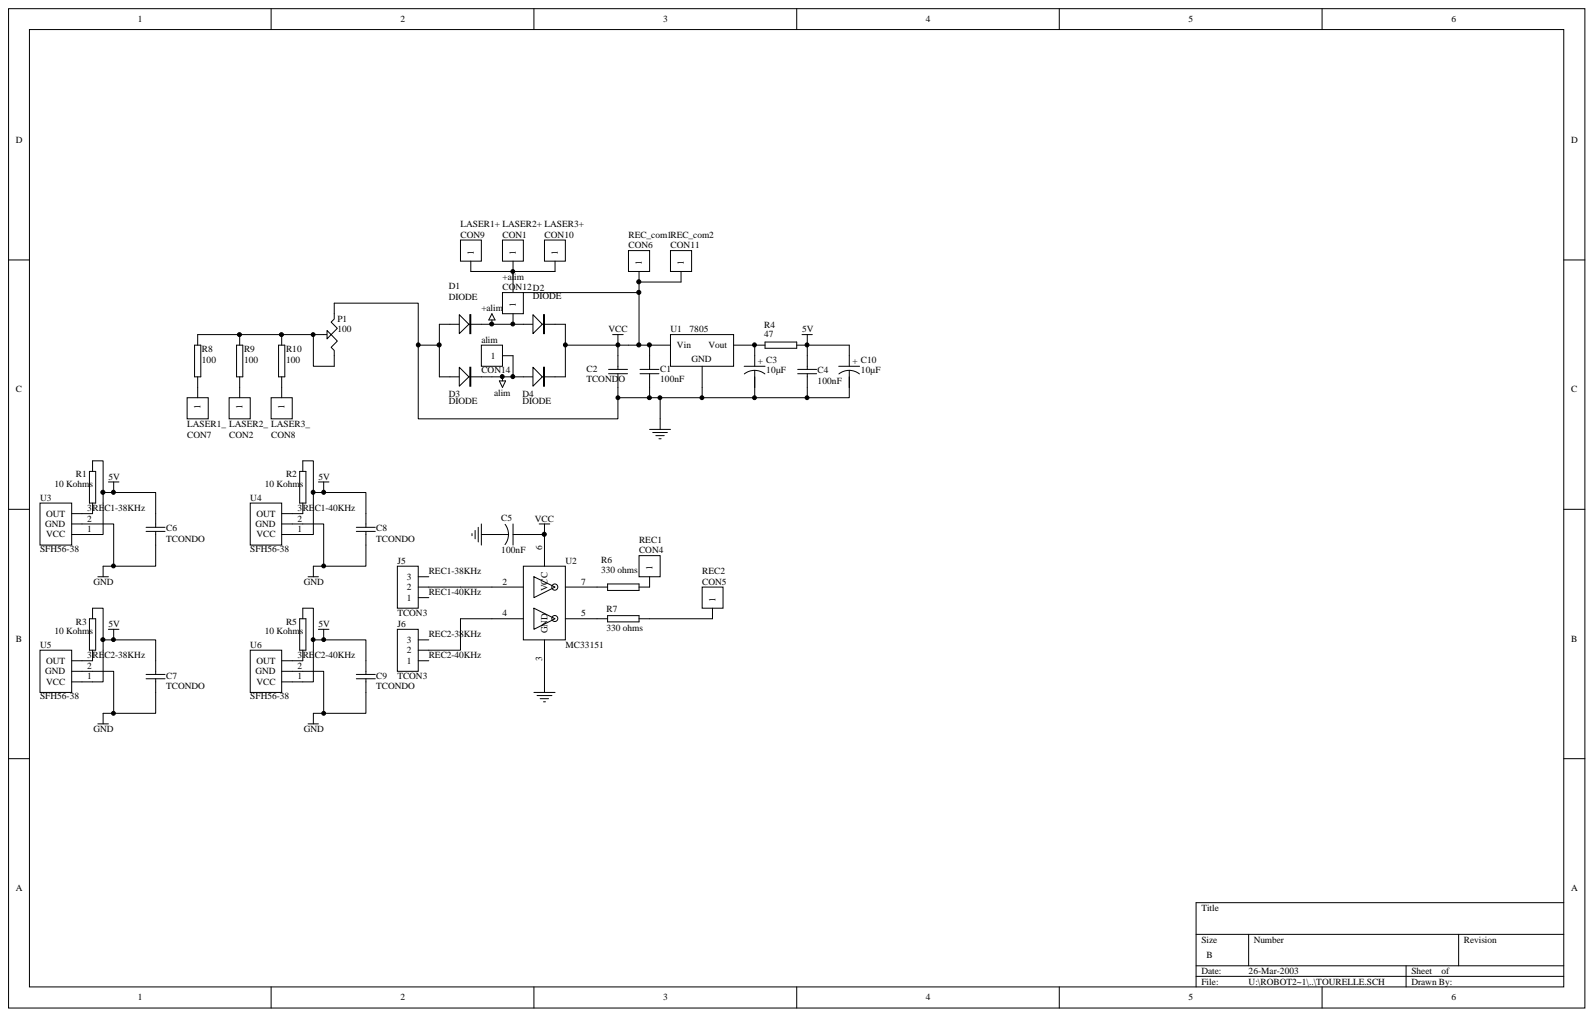
[picture p119: page 1]
