ClubRobotiqueECAM/Balises/Archives/rapport balises/schemas_pdf/pcb/alim4_implantation.pdf

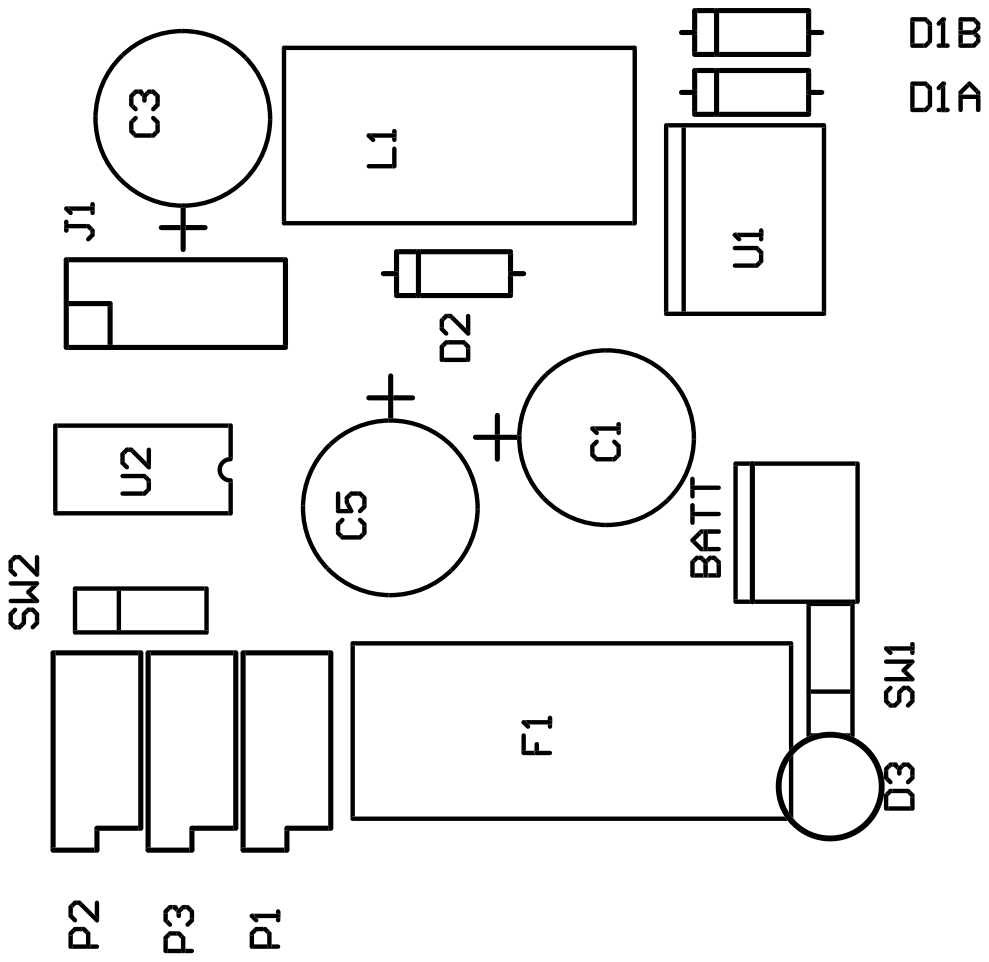
[picture p120: page 1]
