ClubRobotiqueECAM/Balises/Archives/rapport balises/schemas_pdf/pcb/alim4_pistes.pdf

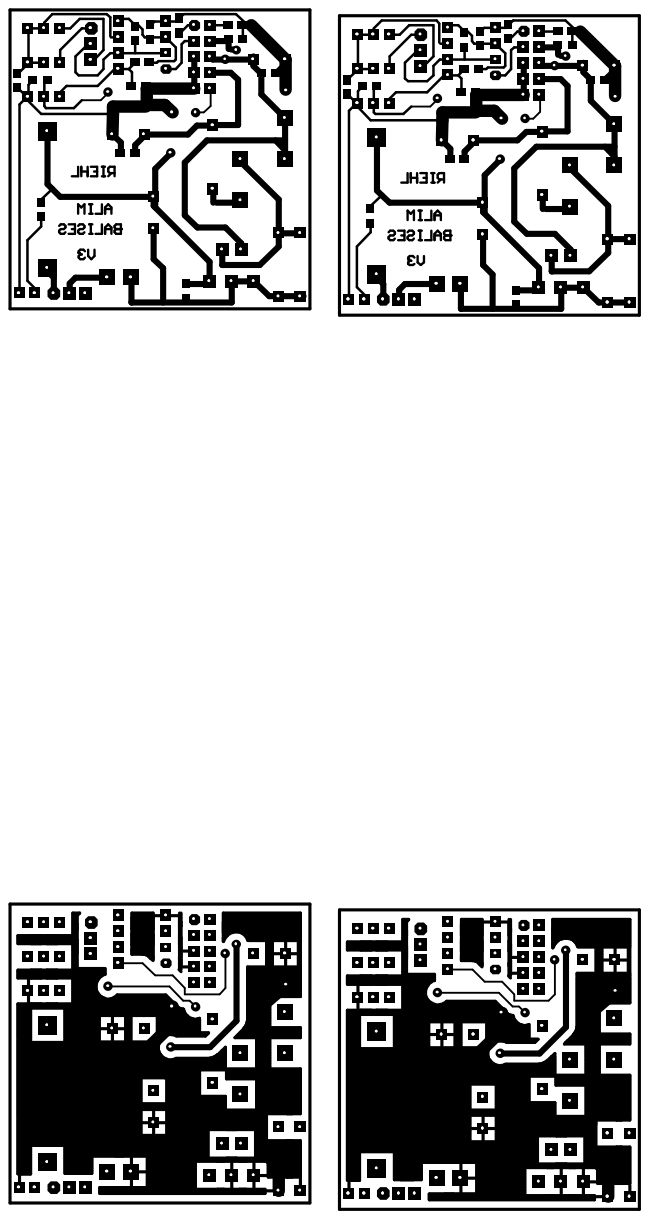
[picture p121: page 1]
