ClubRobotiqueECAM/Balises/Archives/rapport balises/schemas_pdf/pcb/balise_implantation.pdf

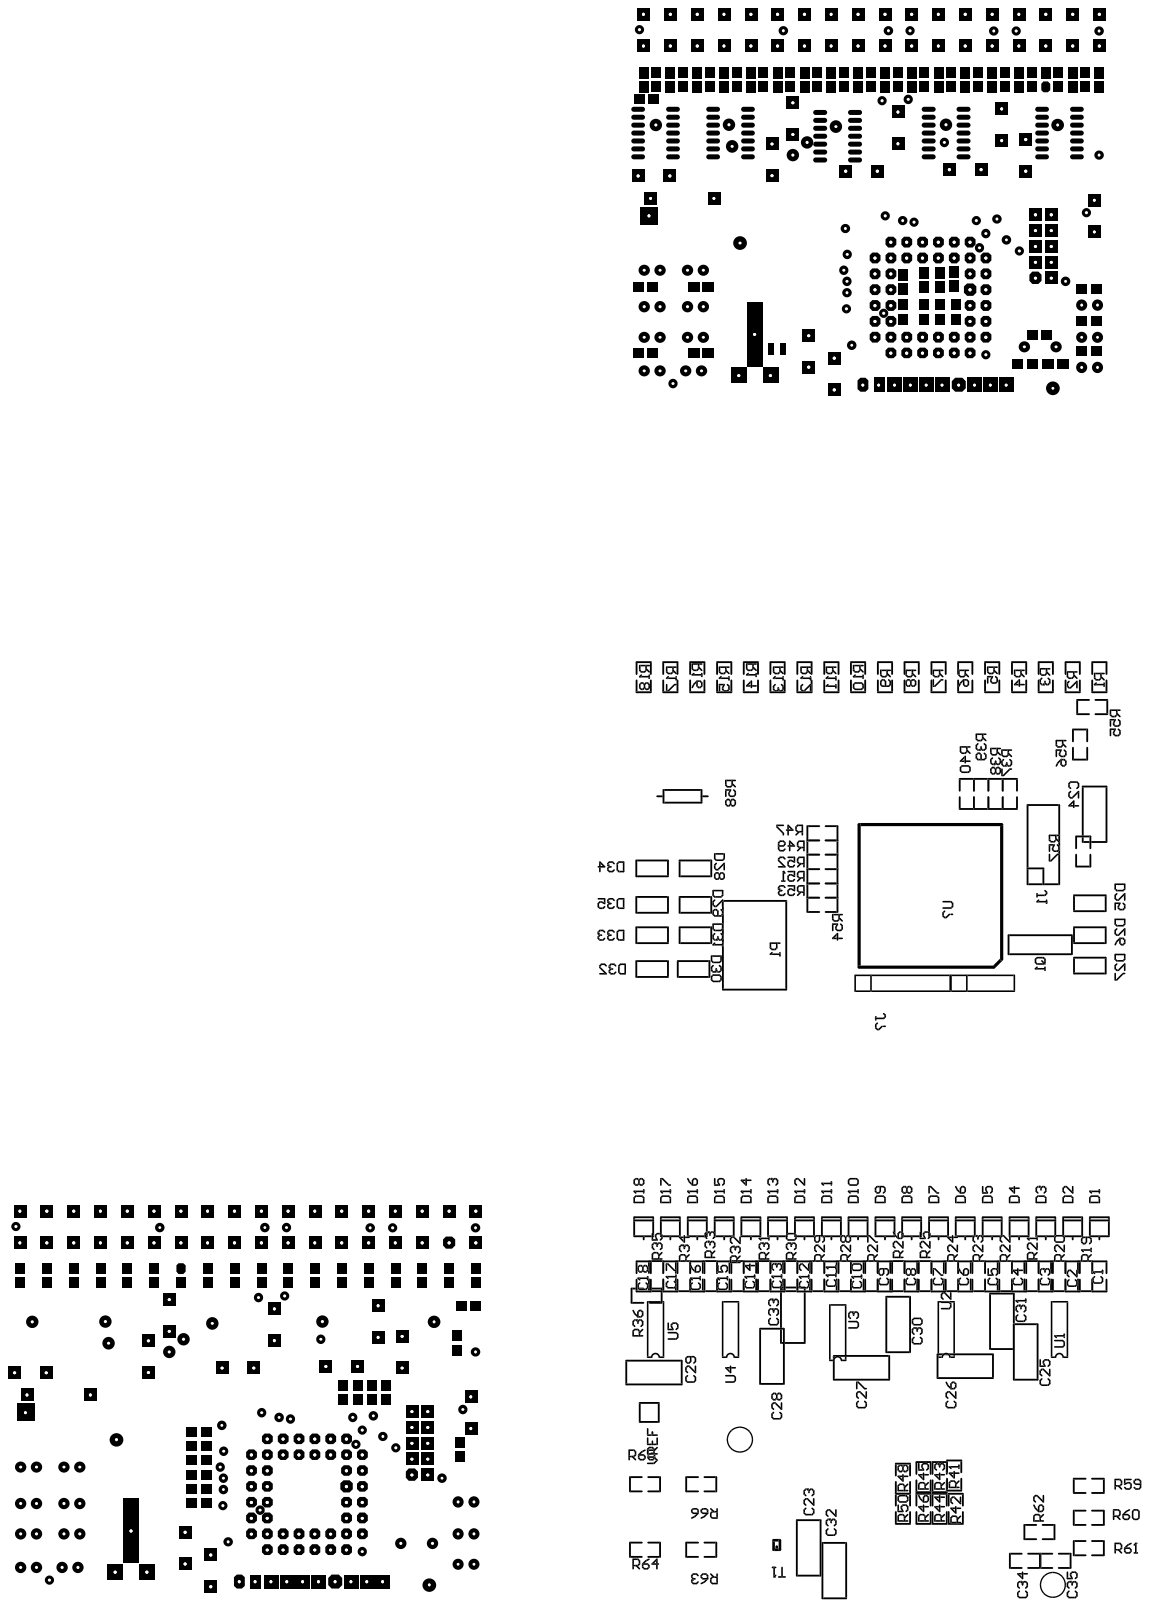
[picture p122: page 1]
