ClubRobotiqueECAM/Balises/Archives/rapport balises/schemas_pdf/pcb/balise_pistes.pdf

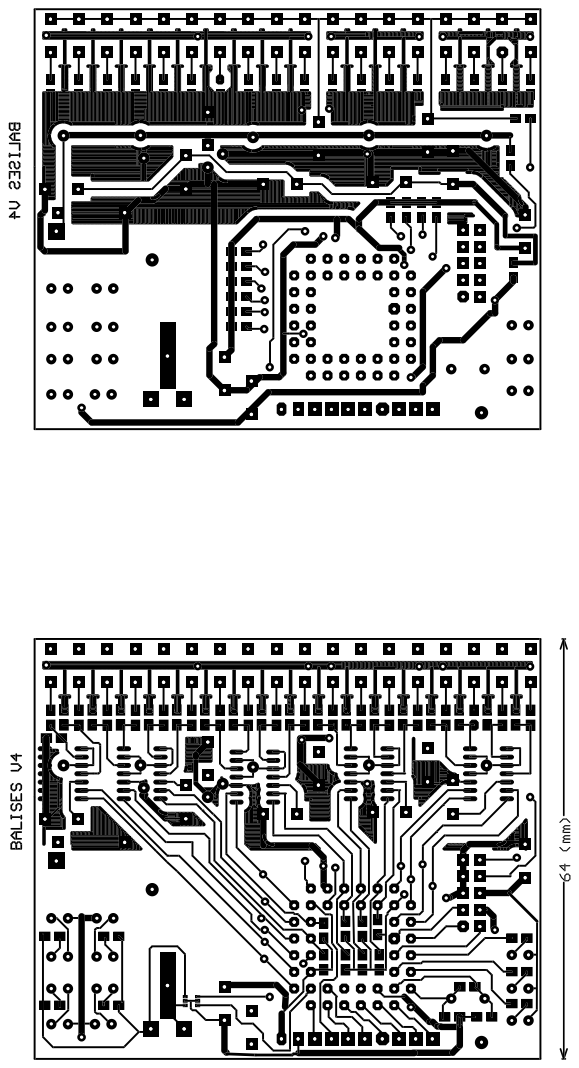
[picture p123: page 1]
