ClubRobotiqueECAM/Balises/Archives/rapport balises/schemas_pdf/pcb/robot_implantation.pdf

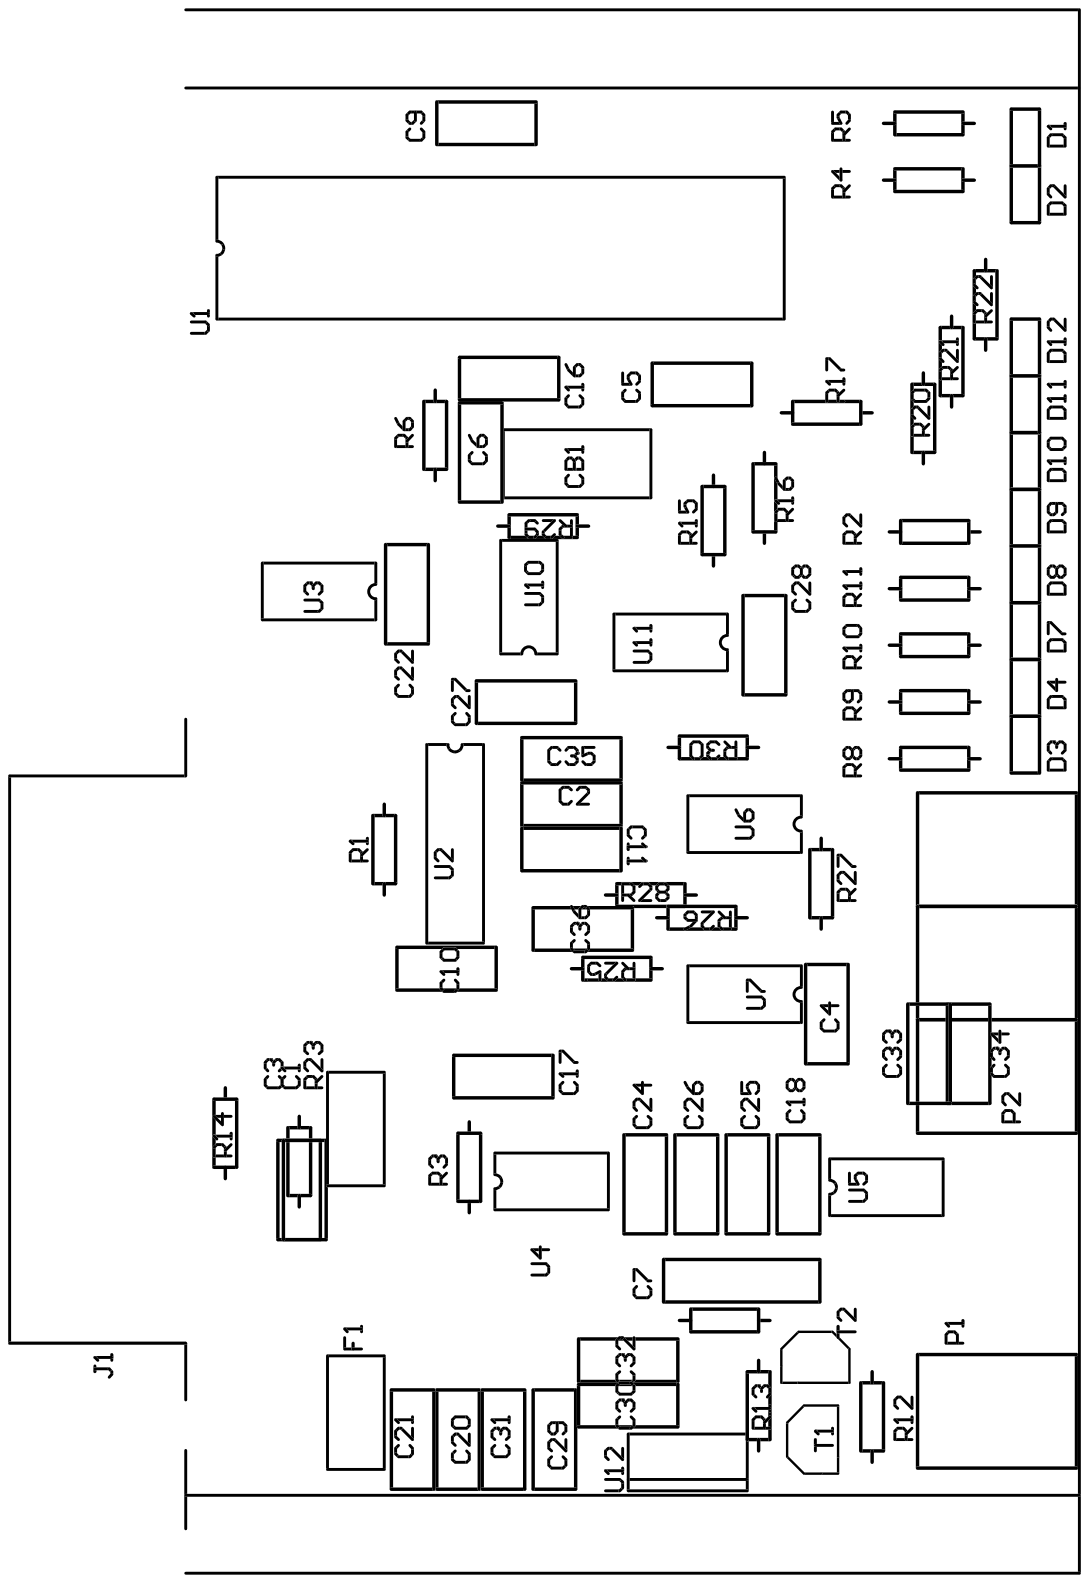
[picture p124: page 1]

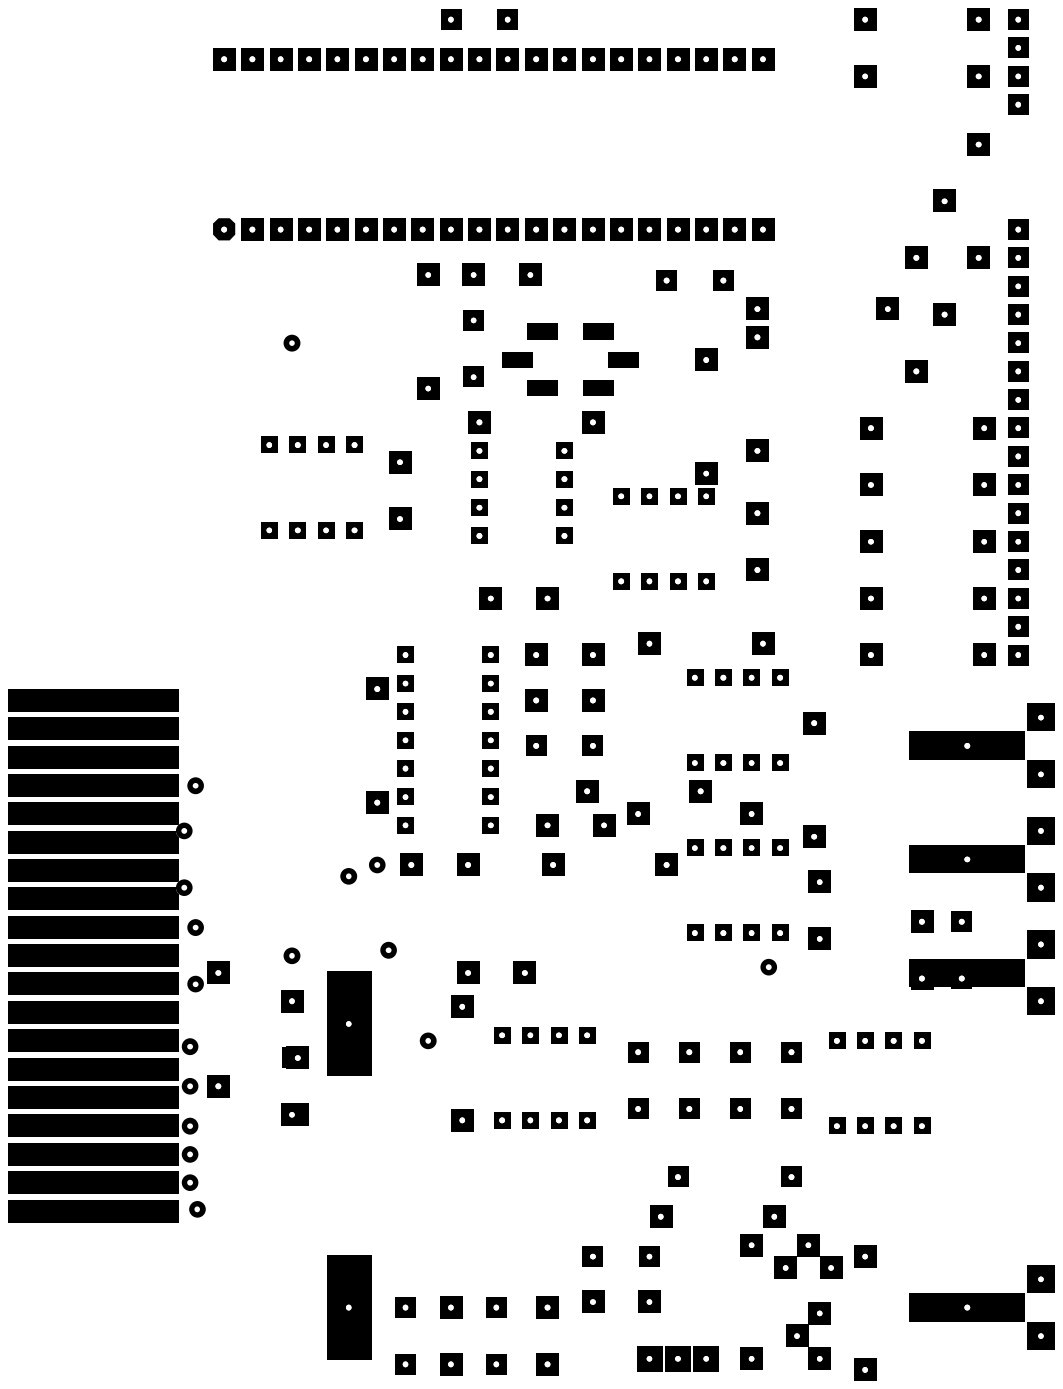
[picture p125: page 3]

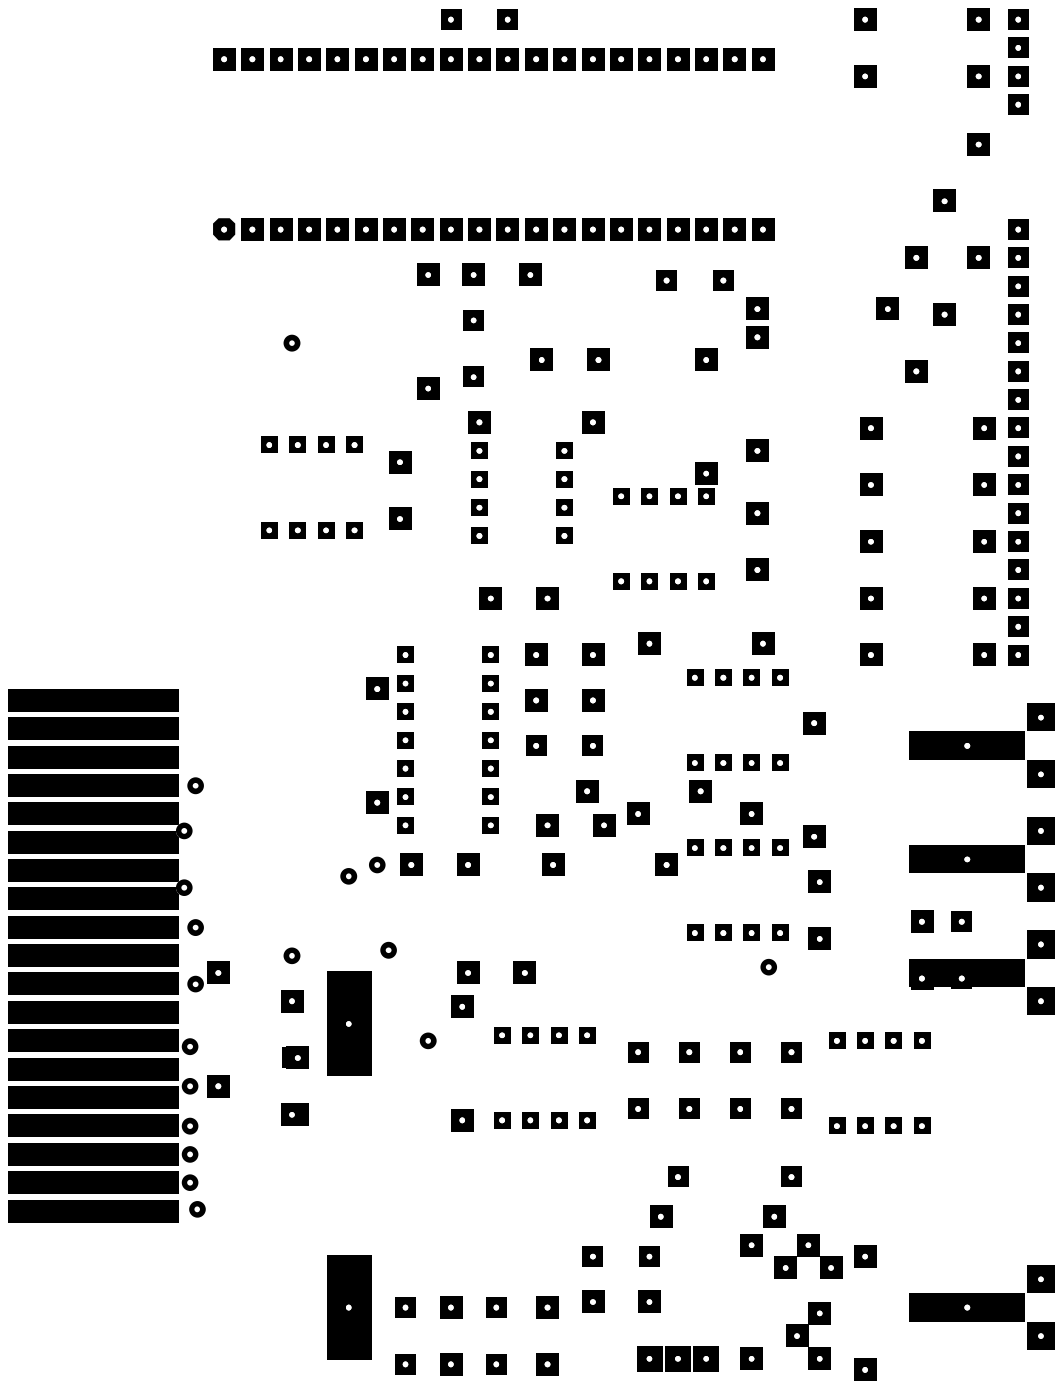
[picture p126: page 4]
