ClubRobotiqueECAM/Balises/Archives/rapport balises/schemas_pdf/pcb/robot_pistes.pdf

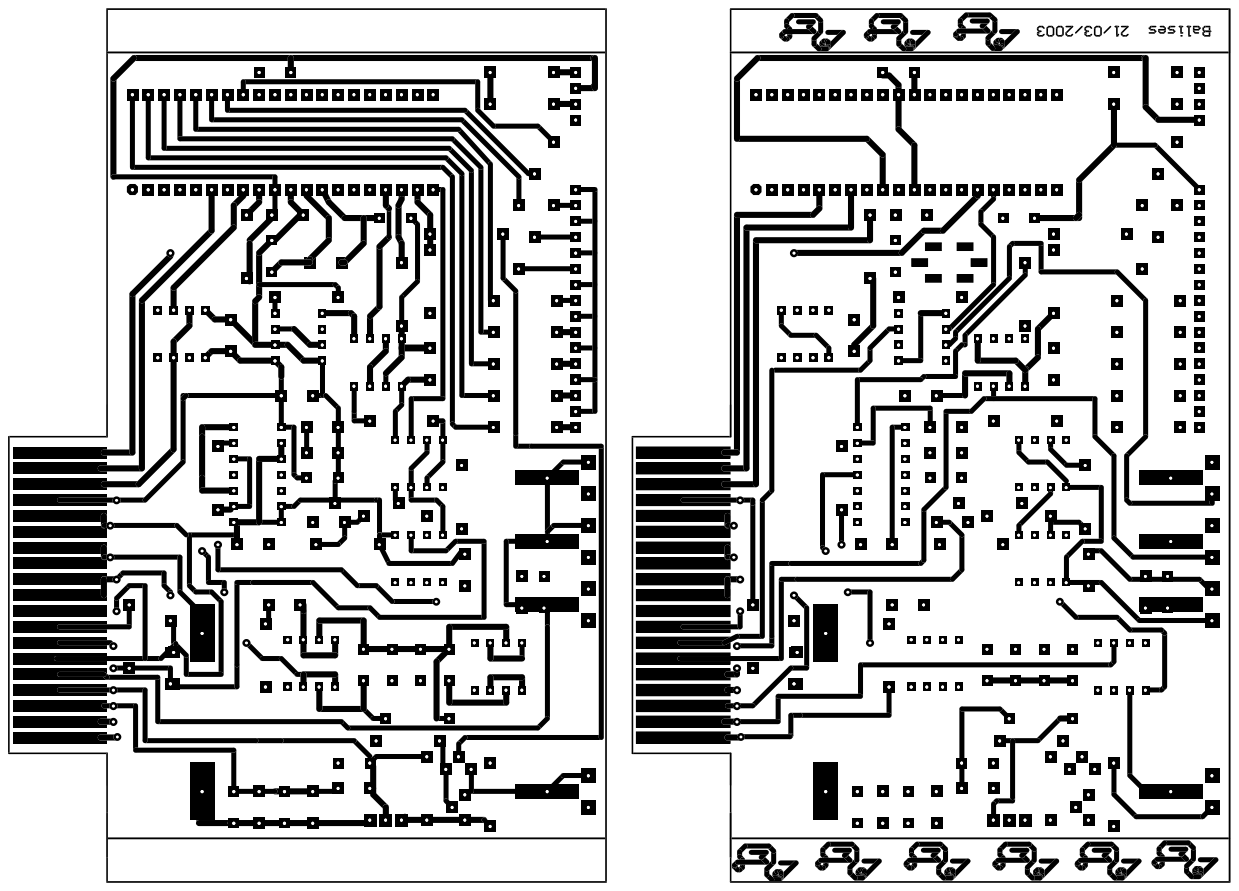
[picture p127: page 1]
