ClubRobotiqueECAM/Balises/Archives/rapport balises/schemas_pdf/pcb/tourelle_implantation.pdf

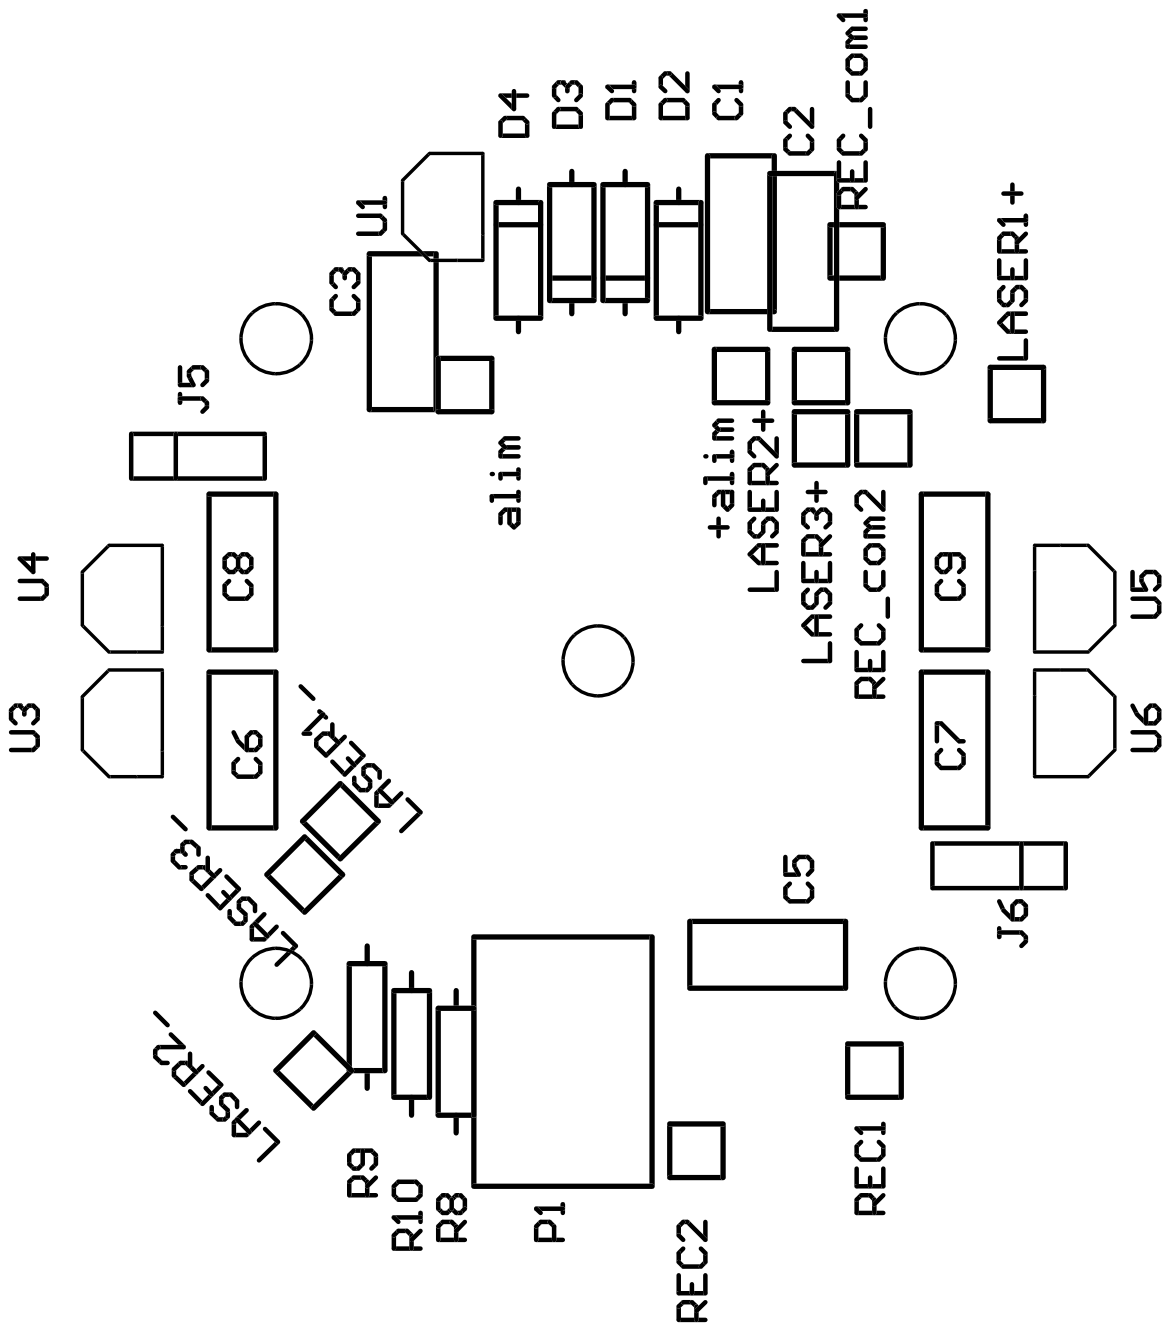
[picture p128: page 1]
