ClubRobotiqueECAM/Balises/Archives/rapport balises/schemas_pdf/pcb/tourelle_pistes.pdf

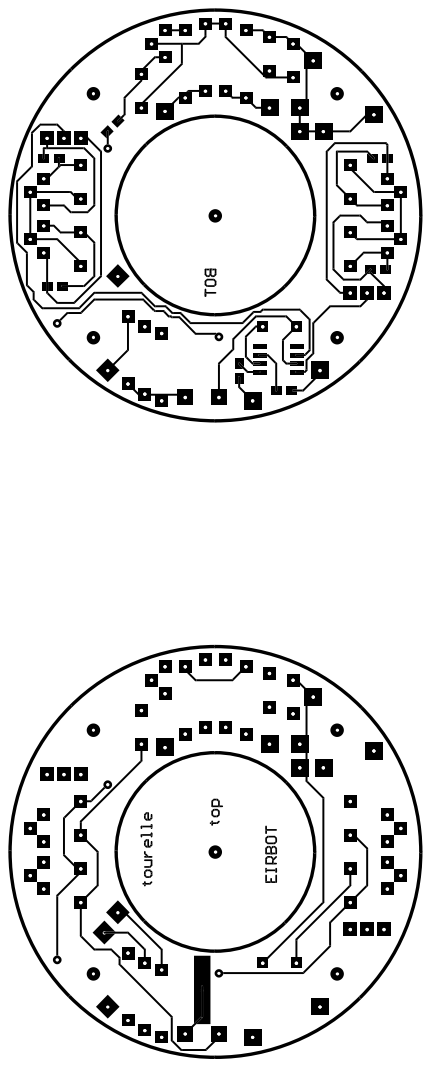
[picture p129: page 1]
